Maniak003/DoZer/Documents/DoZer-current.png

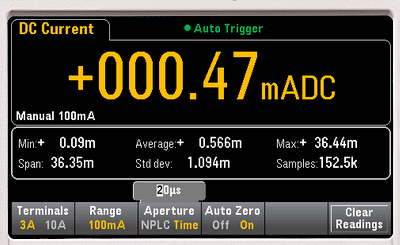
Documents/DoZer-current.png
