Maniak003/DoZer/Documents/DoZer_FSC-BT691.png

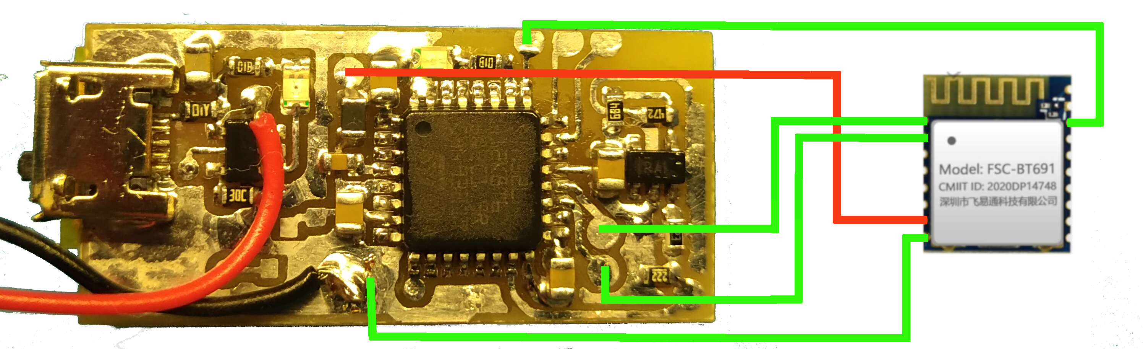
Documents/DoZer_FSC-BT691.png
