Maniak003/DoZer/Documents/IMG_20220416_122035.jpg

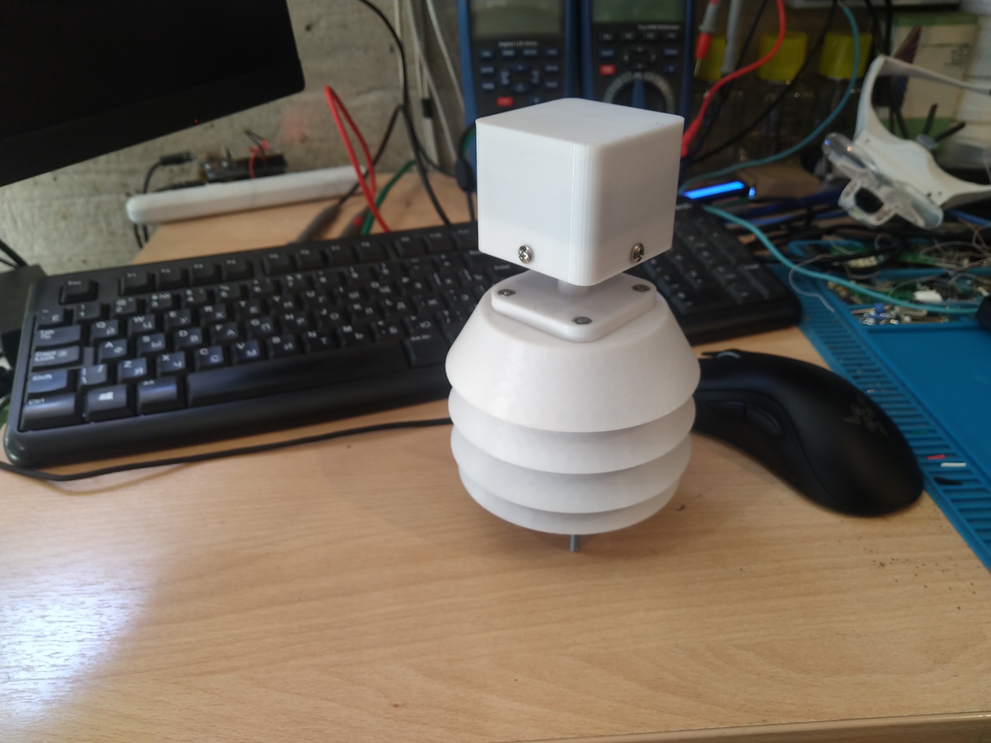
Documents/IMG_20220416_122035.jpg
