Maniak003/DoZer/Documents/LT8410-current.png

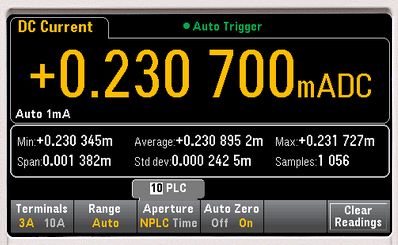
Documents/LT8410-current.png
