Maniak003/DoZer/Documents/Screenshot_20221201-142426.png

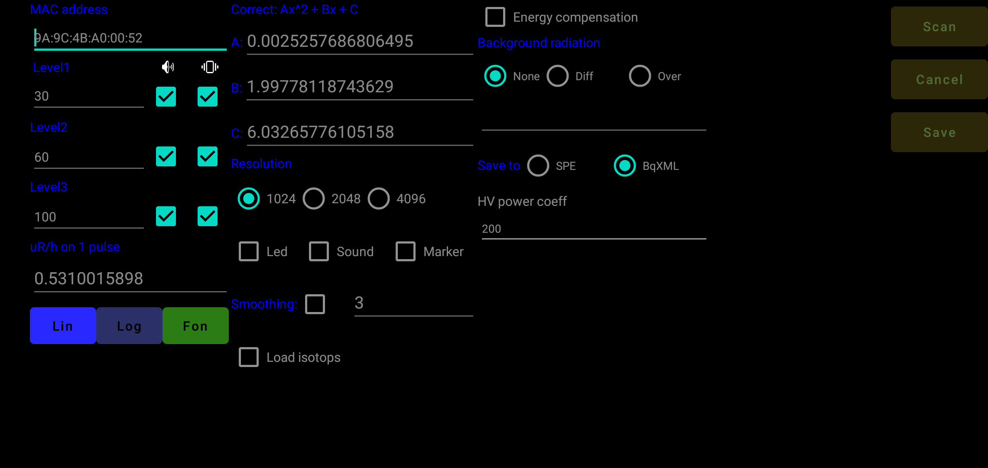
Documents/Screenshot_20221201-142426.png
