Maniak003/DoZer/picture/2023_03_03_14_29_00_972.png

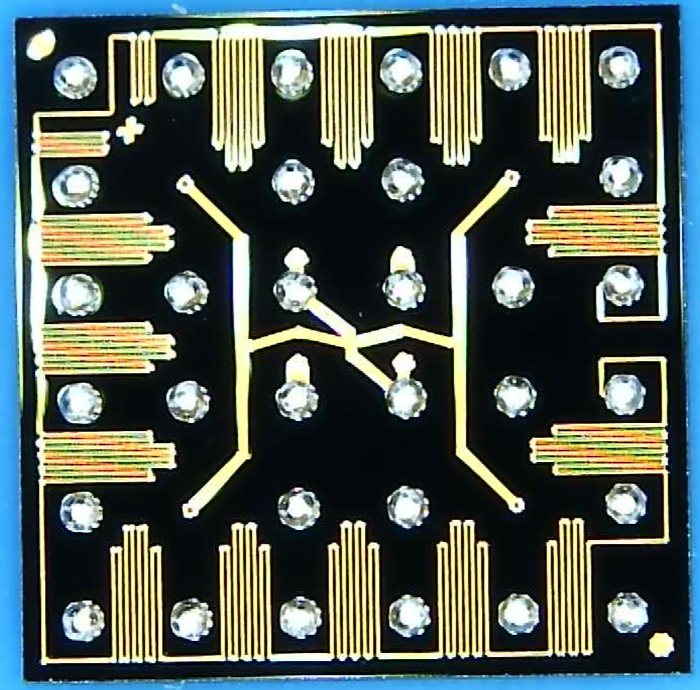
picture/2023_03_03_14_29_00_972.png
