Maniak003/DoZer/picture/2023_03_03_14_31_07_471.png

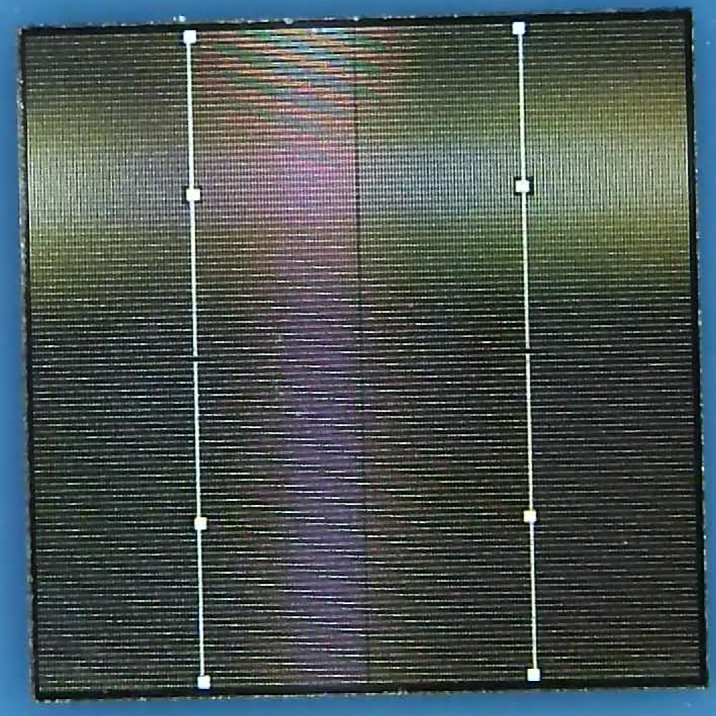
picture/2023_03_03_14_31_07_471.png
