Maniak003/DoZer/picture/DoZer_JDY-19.png

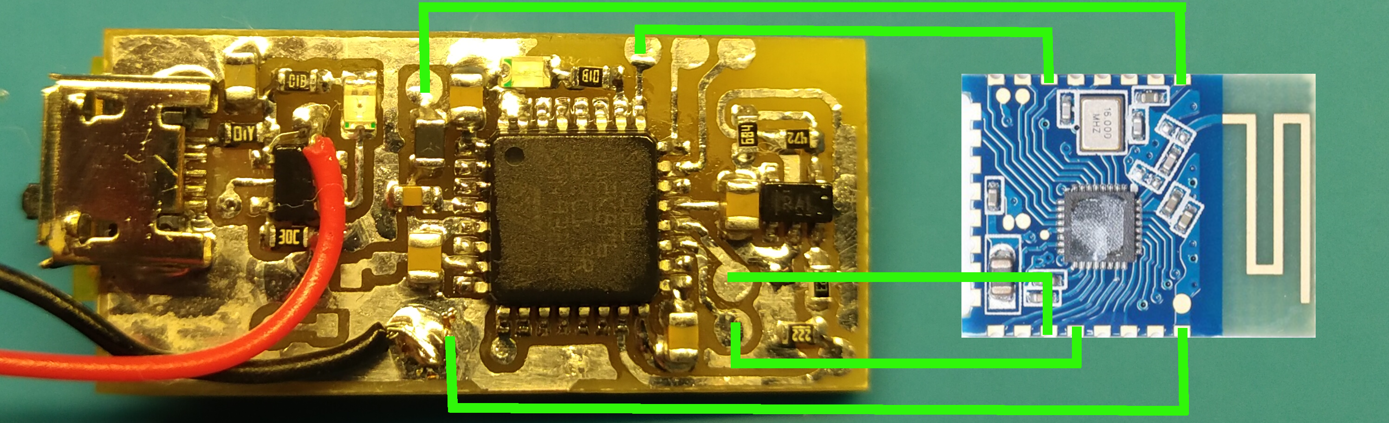
picture/DoZer_JDY-19.png
