Maniak003/DoZer/picture/IMG_20200828_080617.jpg

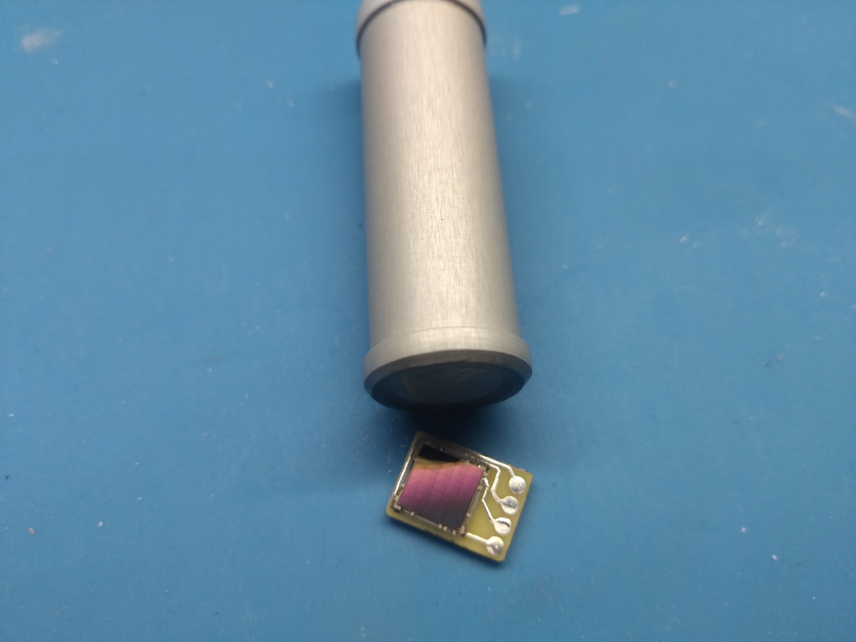
picture/IMG_20200828_080617.jpg
