Maniak003/DoZer/picture/IMG_20201008_110059.jpg

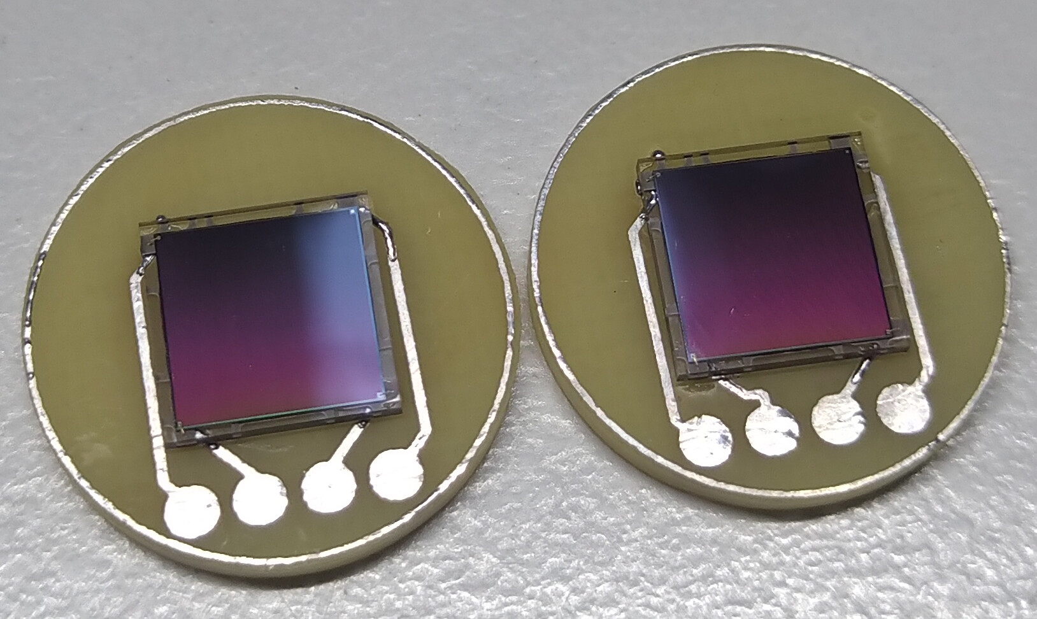
picture/IMG_20201008_110059.jpg
