Maniak003/DoZer/picture/IMG_20201029_205514.jpg

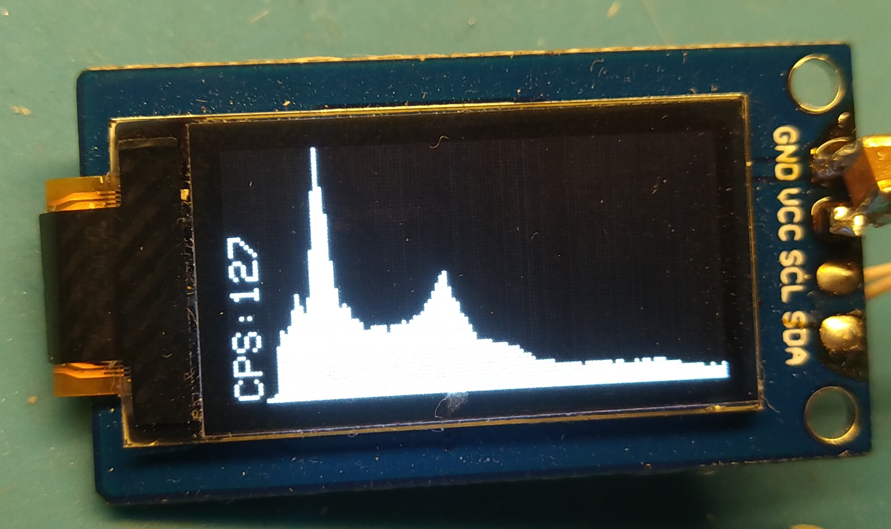
picture/IMG_20201029_205514.jpg
