Maniak003/DoZer/picture/IMG_20201205_212949.jpg

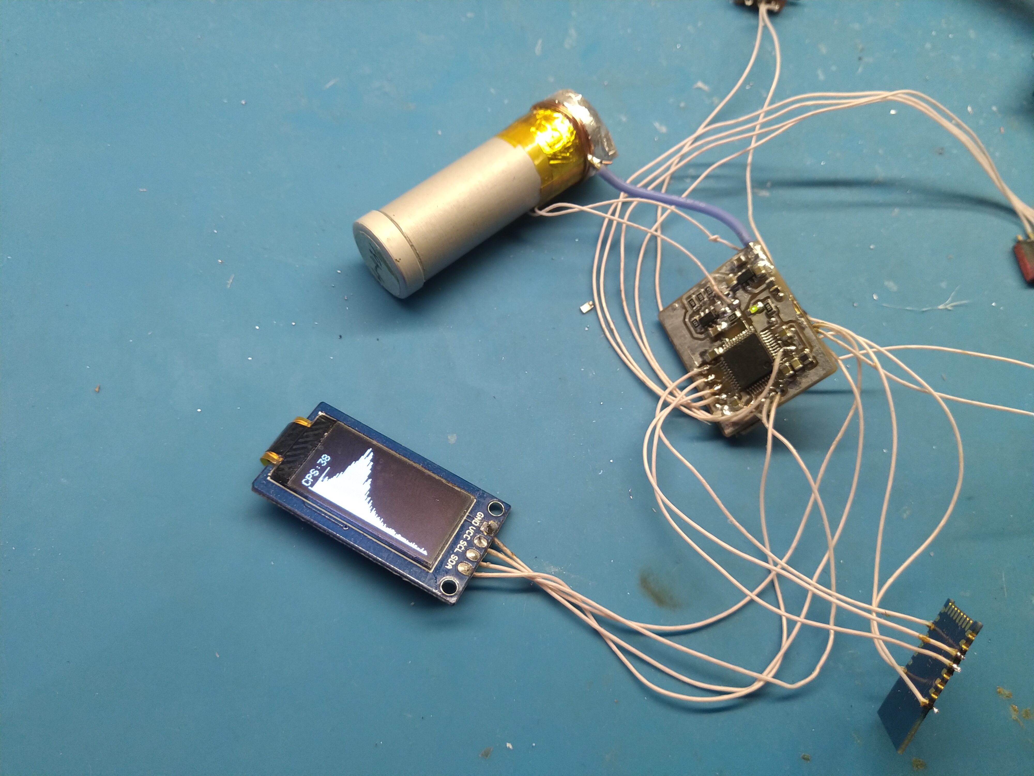
picture/IMG_20201205_212949.jpg
