Maniak003/DoZer/picture/IMG_20201224_195748.jpg

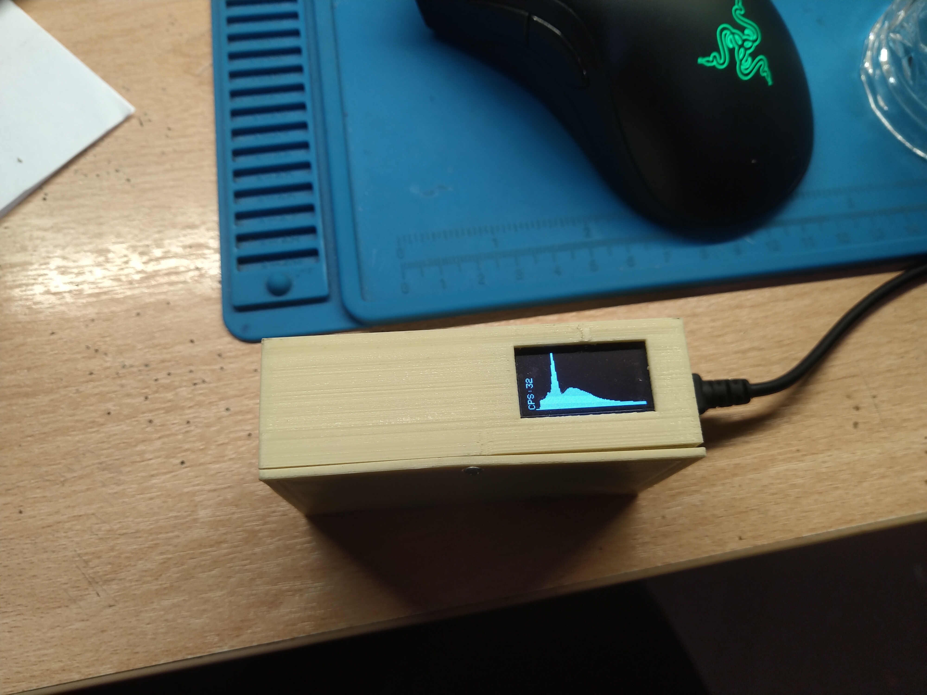
picture/IMG_20201224_195748.jpg
