Maniak003/DoZer/picture/IMG_20210123_151214.jpg

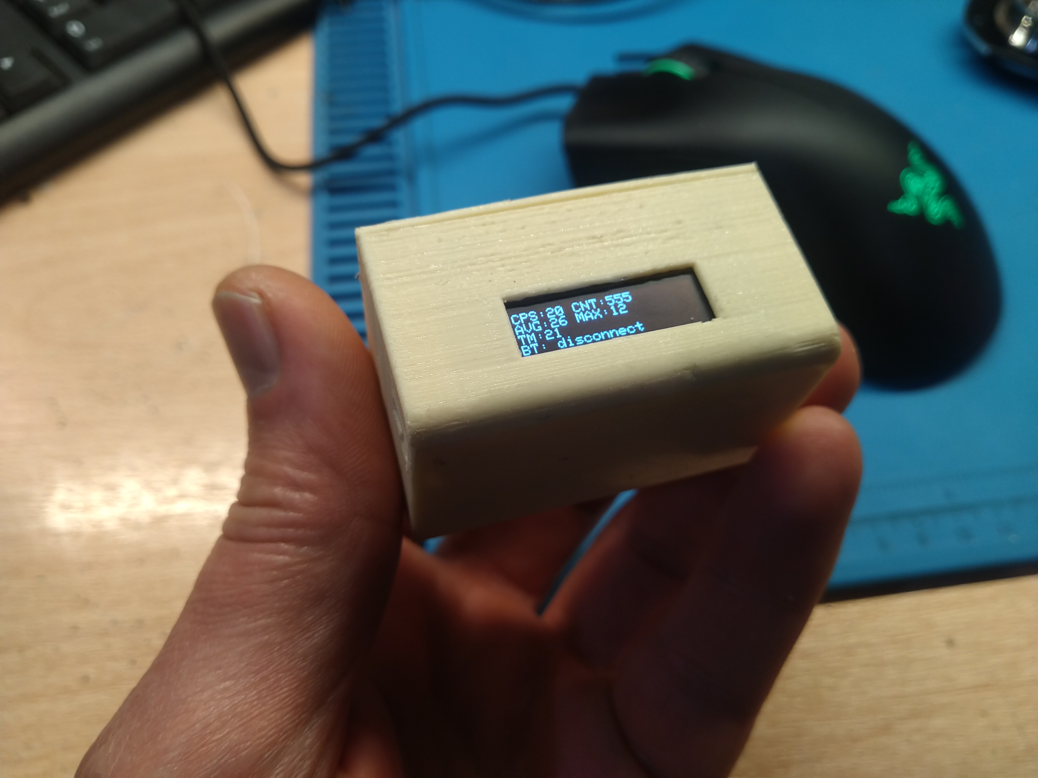
picture/IMG_20210123_151214.jpg
