Maniak003/DoZer/picture/IMG_20210207_145107.jpg

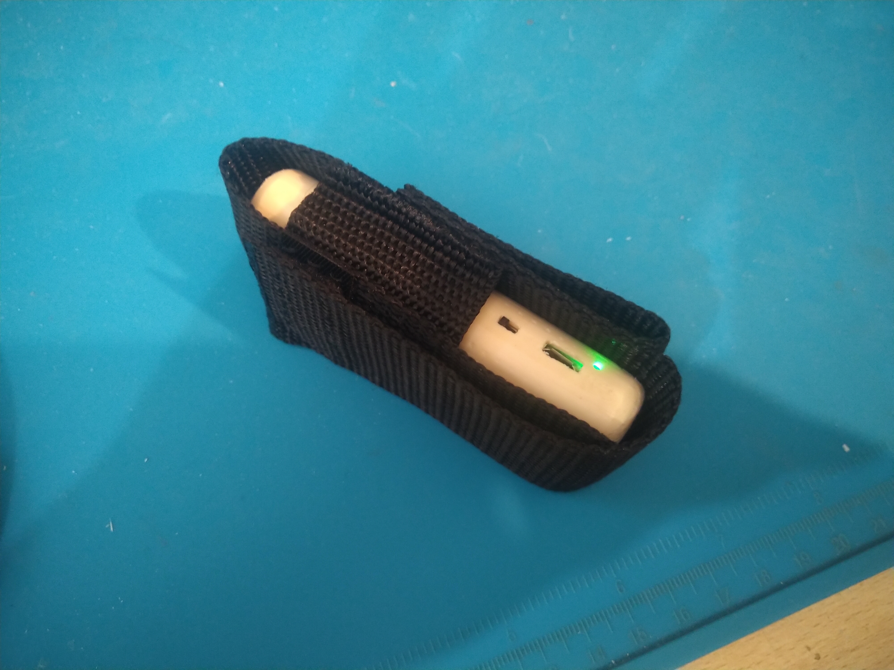
picture/IMG_20210207_145107.jpg
