Maniak003/DoZer/picture/IMG_20210209_133956.jpg

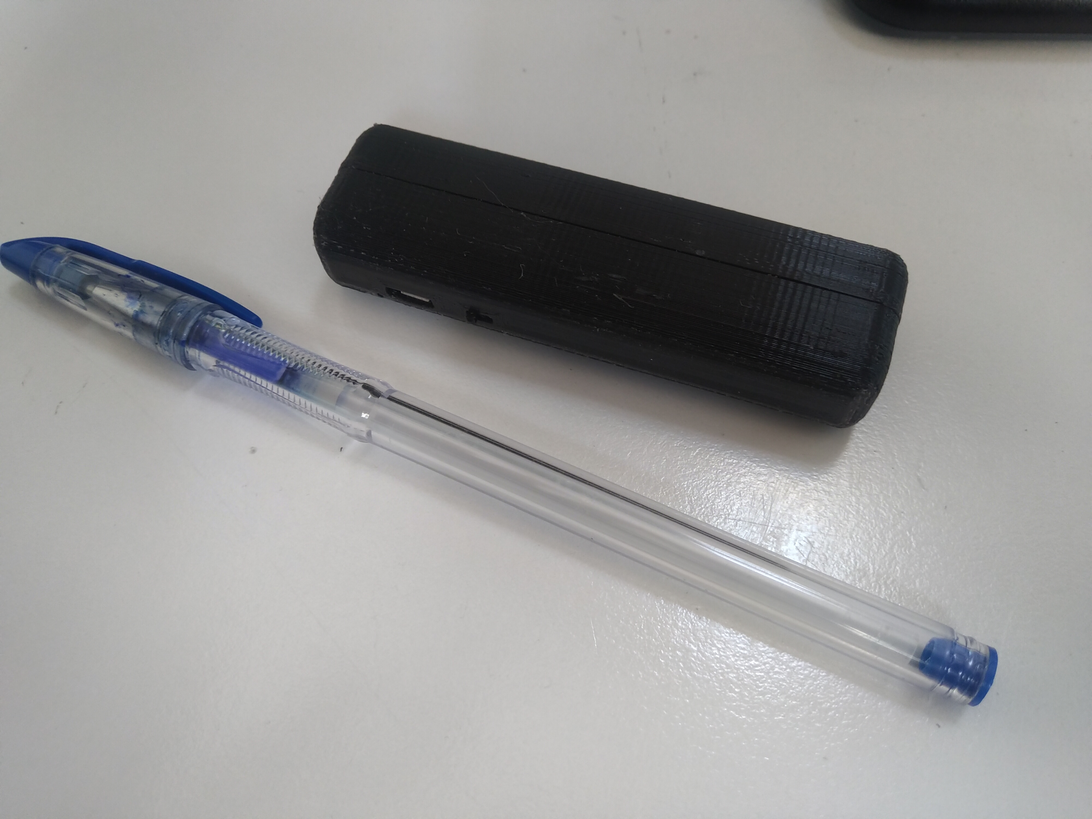
picture/IMG_20210209_133956.jpg
