Maniak003/DoZer/picture/IMG_20210417_190906.jpg

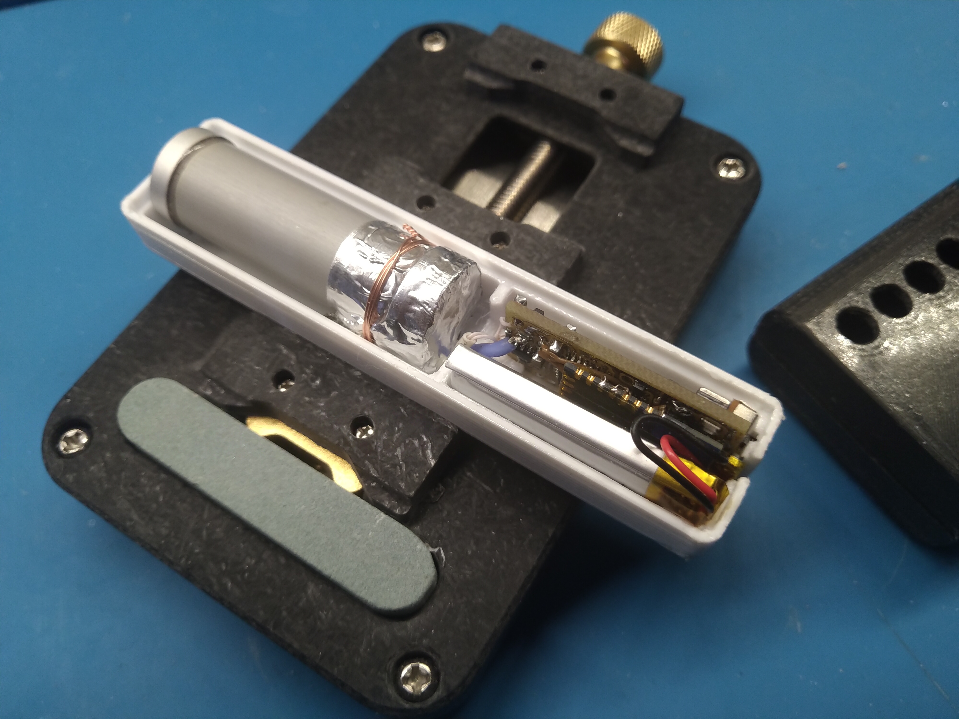
picture/IMG_20210417_190906.jpg
