Maniak003/DoZer/picture/IMG_20210417_202949.jpg

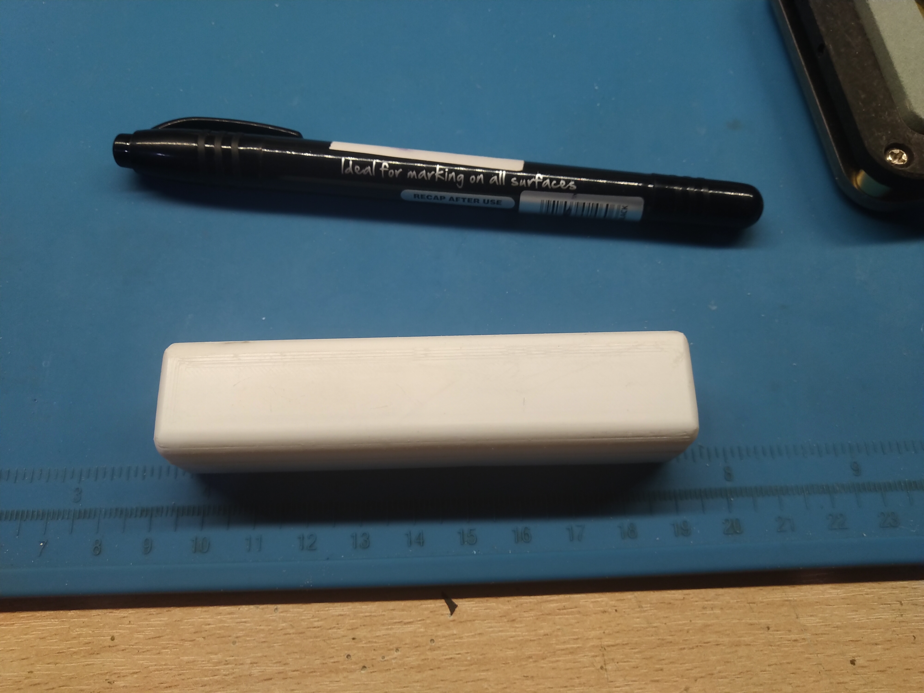
picture/IMG_20210417_202949.jpg
