Maniak003/DoZer/picture/IMG_20210425_131545.jpg

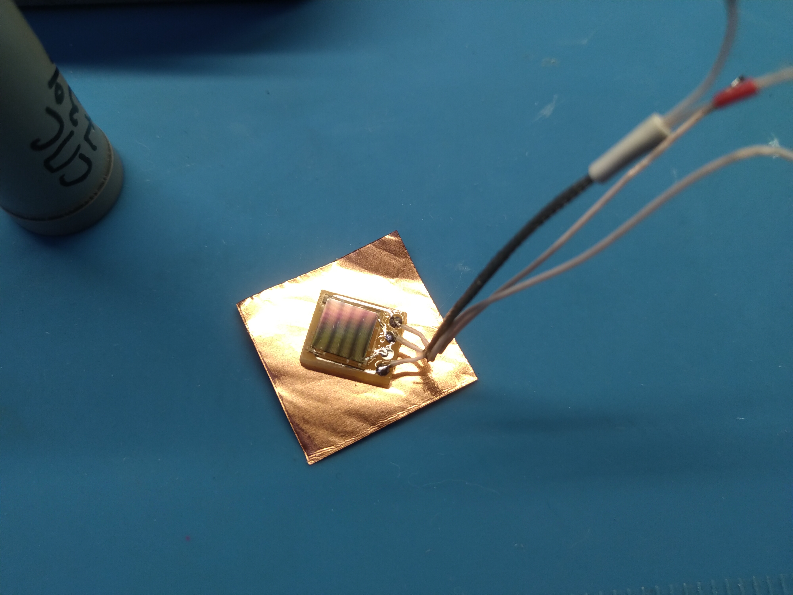
picture/IMG_20210425_131545.jpg
