Maniak003/DoZer/picture/IMG_20210425_131629.jpg

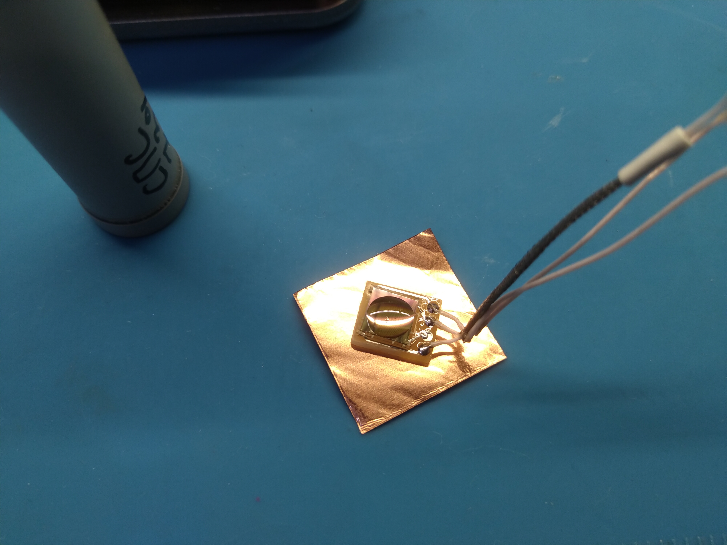
picture/IMG_20210425_131629.jpg
