Maniak003/DoZer/picture/IMG_20210425_131818.jpg

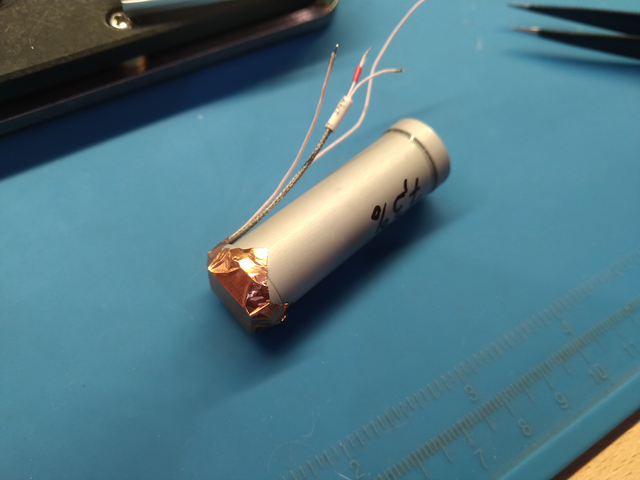
picture/IMG_20210425_131818.jpg
