Maniak003/DoZer/picture/IMG_20210425_132600.jpg

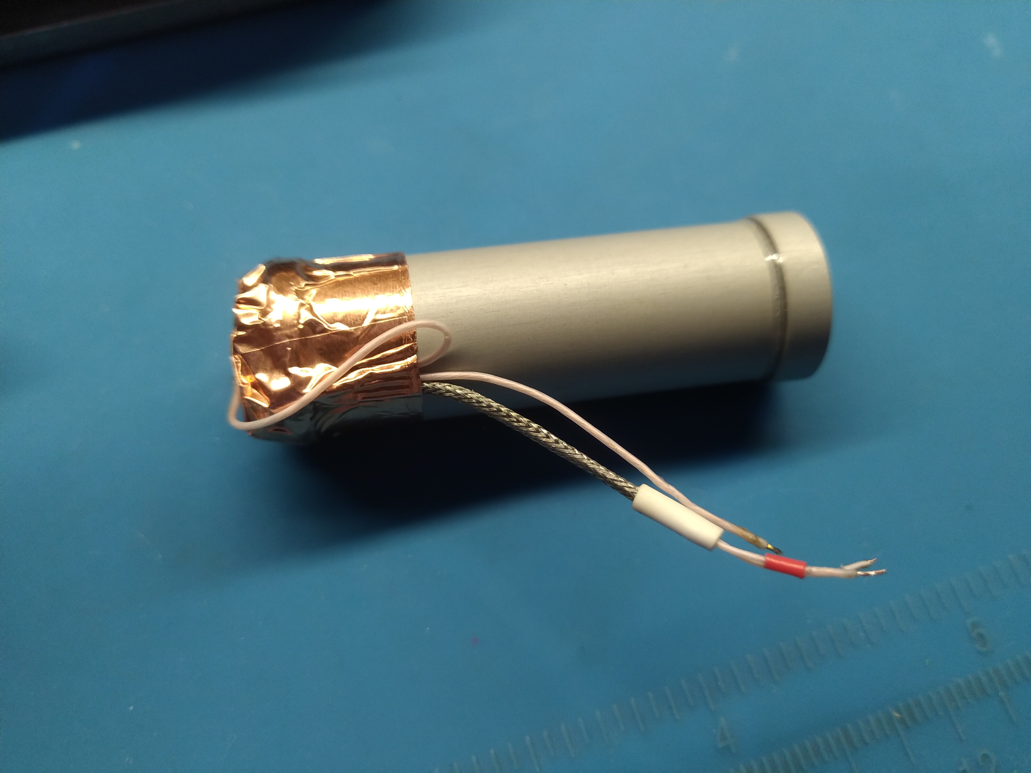
picture/IMG_20210425_132600.jpg
