Maniak003/DoZer/picture/IMG_20210530_200147.jpg

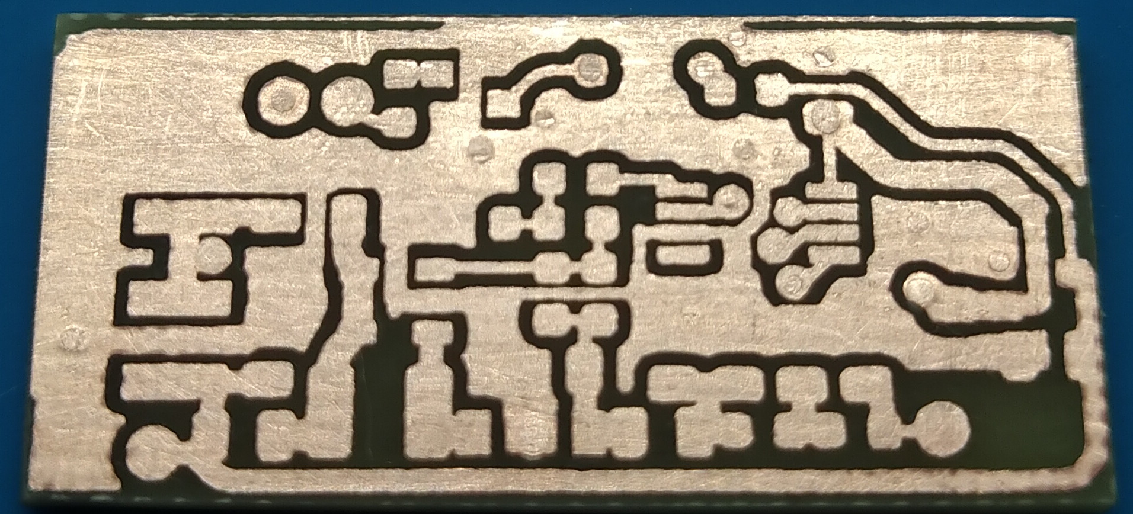
picture/IMG_20210530_200147.jpg
