Maniak003/DoZer/picture/IMG_20210530_200202.jpg

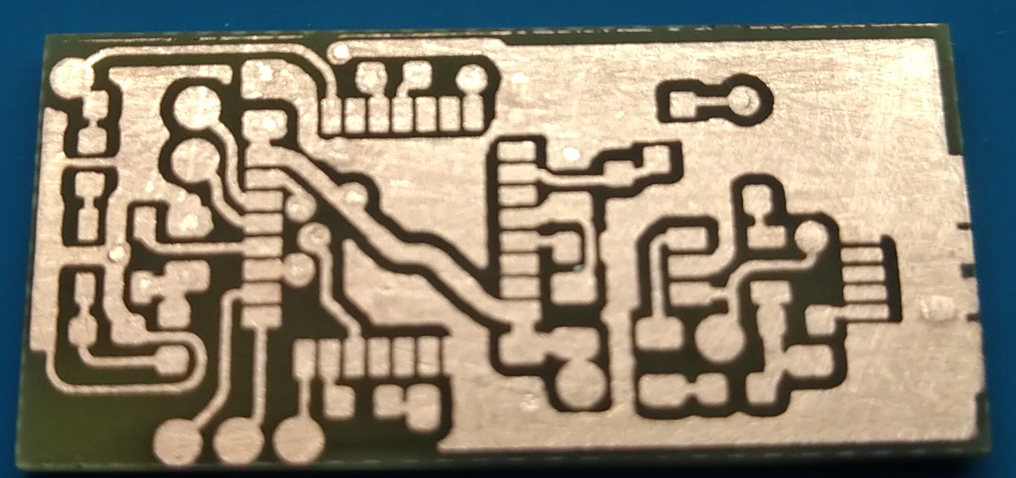
picture/IMG_20210530_200202.jpg
