Maniak003/DoZer/picture/IMG_20210603_091119_317.jpg

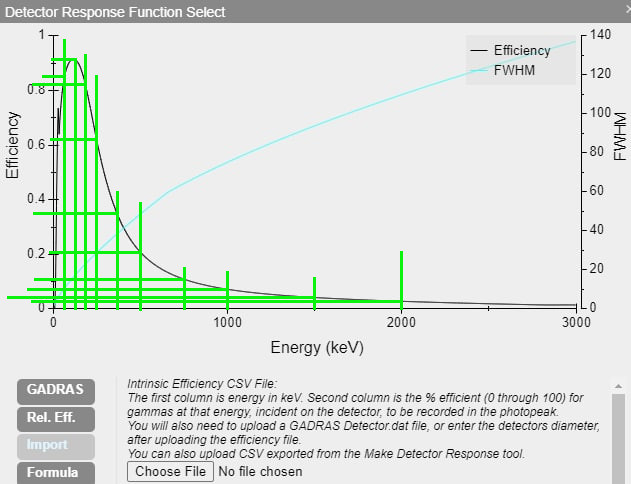
picture/IMG_20210603_091119_317.jpg
