Maniak003/DoZer/picture/IMG_20210627_105556.jpg

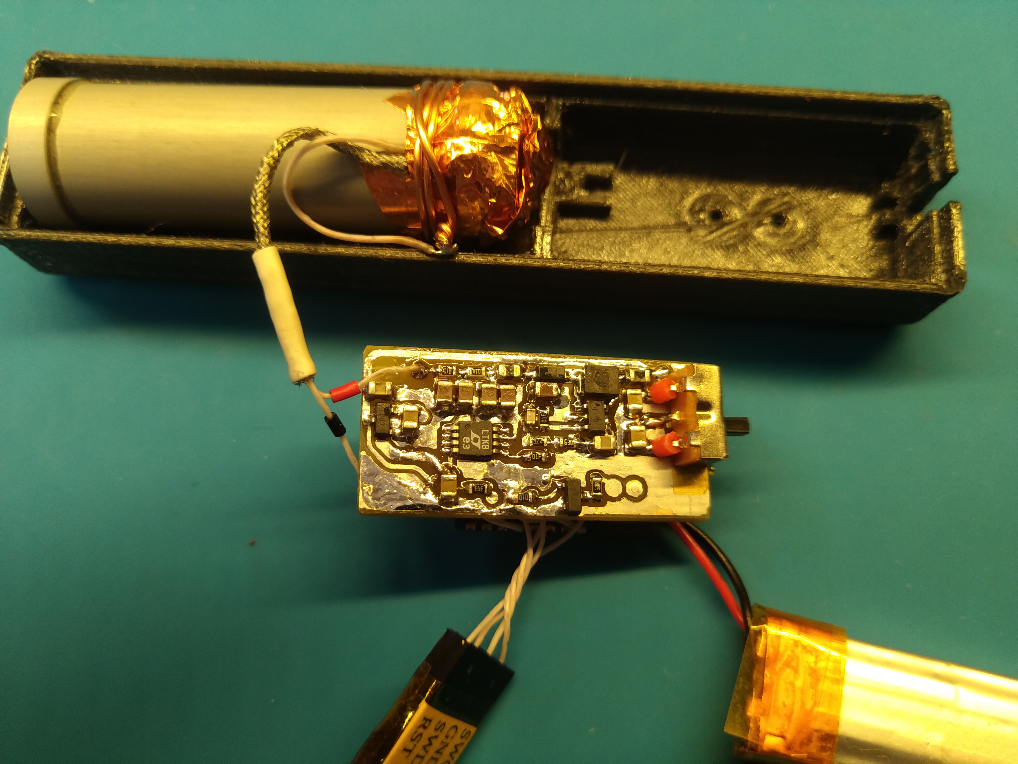
picture/IMG_20210627_105556.jpg
