Maniak003/DoZer/picture/IMG_20210627_110533.jpg

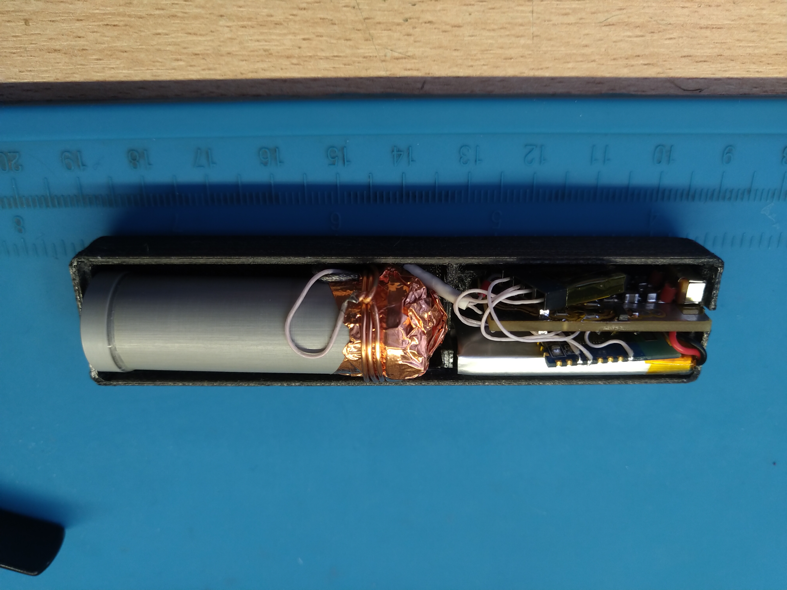
picture/IMG_20210627_110533.jpg
