Maniak003/DoZer/picture/IMG_20210627_110743.jpg

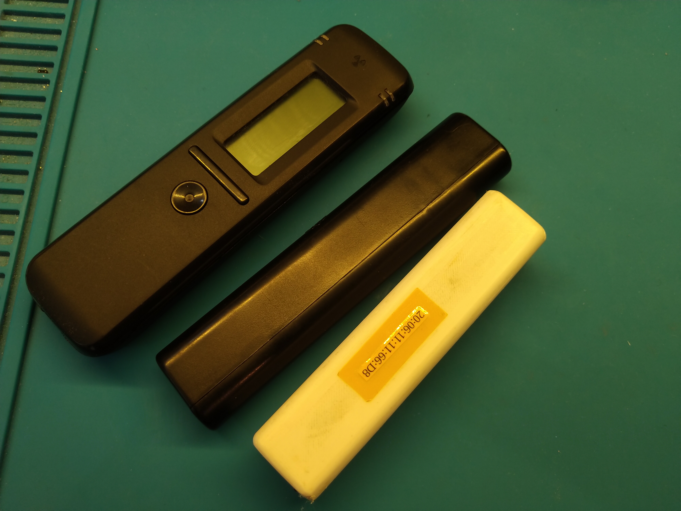
picture/IMG_20210627_110743.jpg
