Maniak003/DoZer/picture/IMG_20210912_121010.jpg

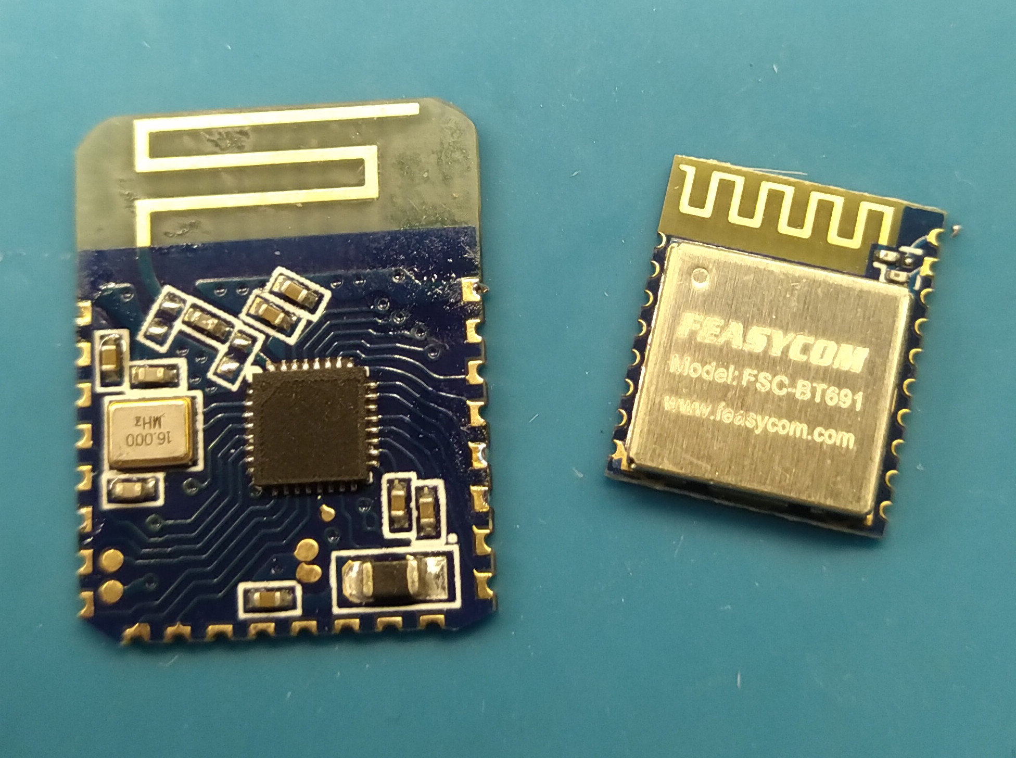
picture/IMG_20210912_121010.jpg
