Maniak003/DoZer/picture/IMG_20211003_150513.jpg

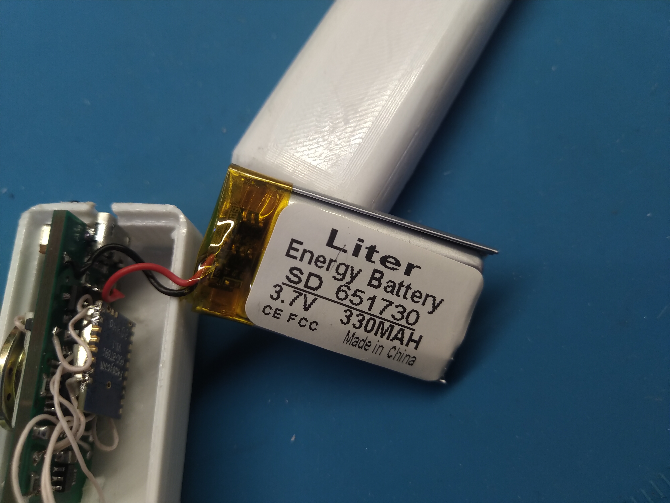
picture/IMG_20211003_150513.jpg
