Maniak003/DoZer/picture/IMG_20211003_150646.jpg

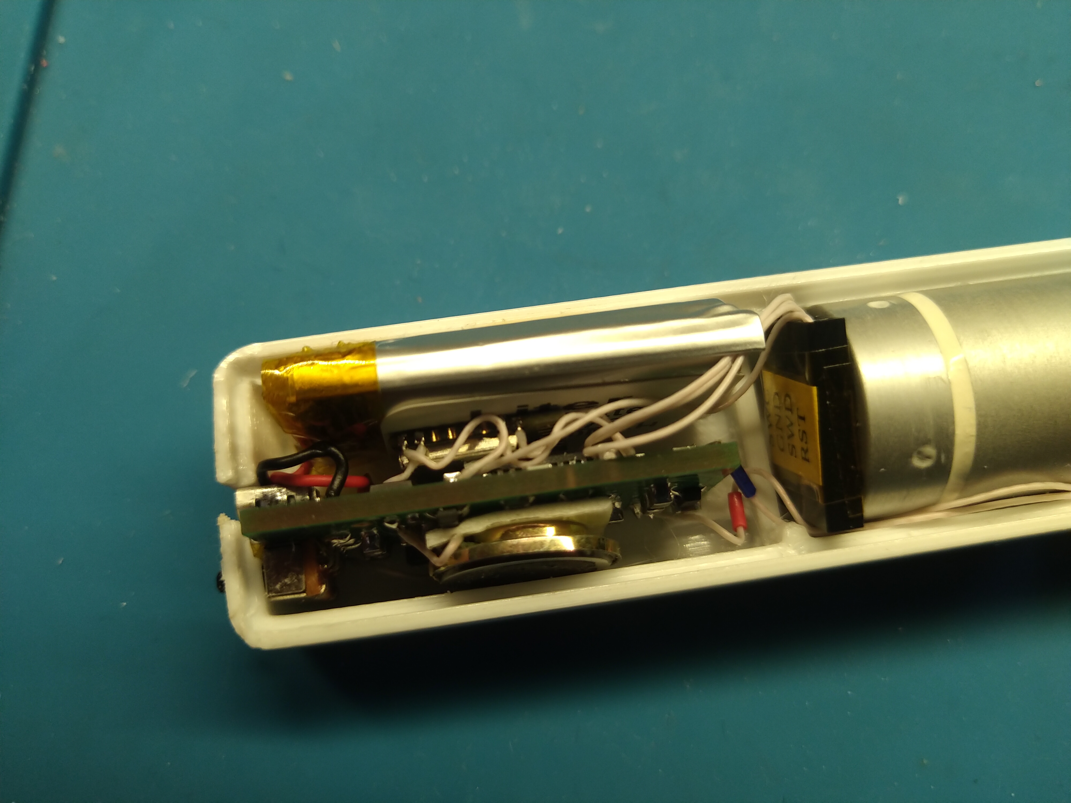
picture/IMG_20211003_150646.jpg
