Maniak003/DoZer/picture/IMG_20211007_115434.jpg

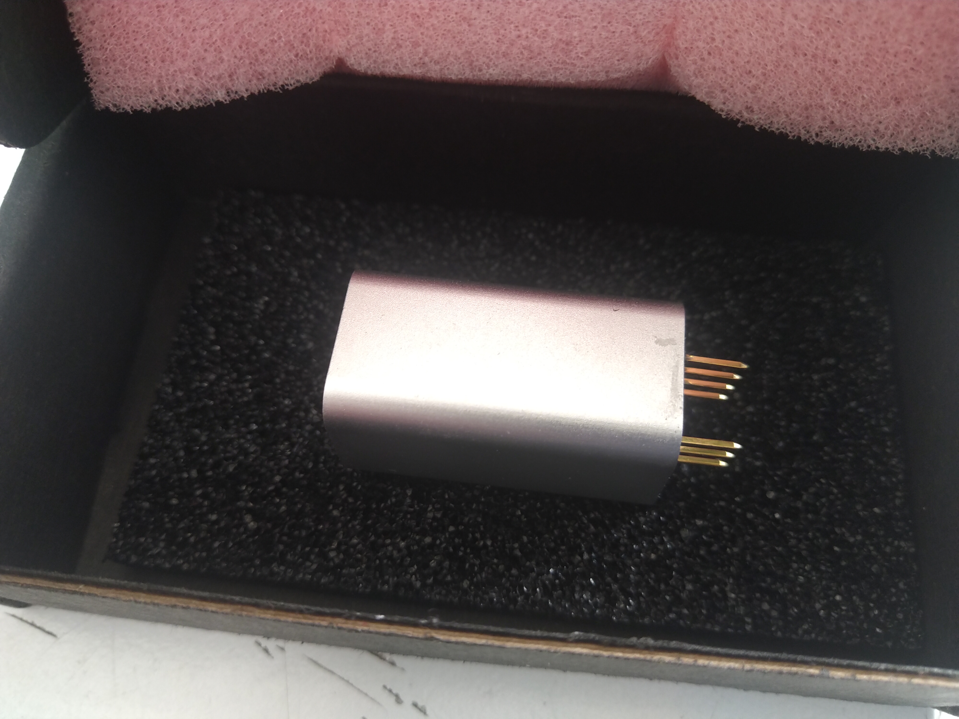
picture/IMG_20211007_115434.jpg
