Maniak003/DoZer/picture/IMG_20211007_115442.jpg

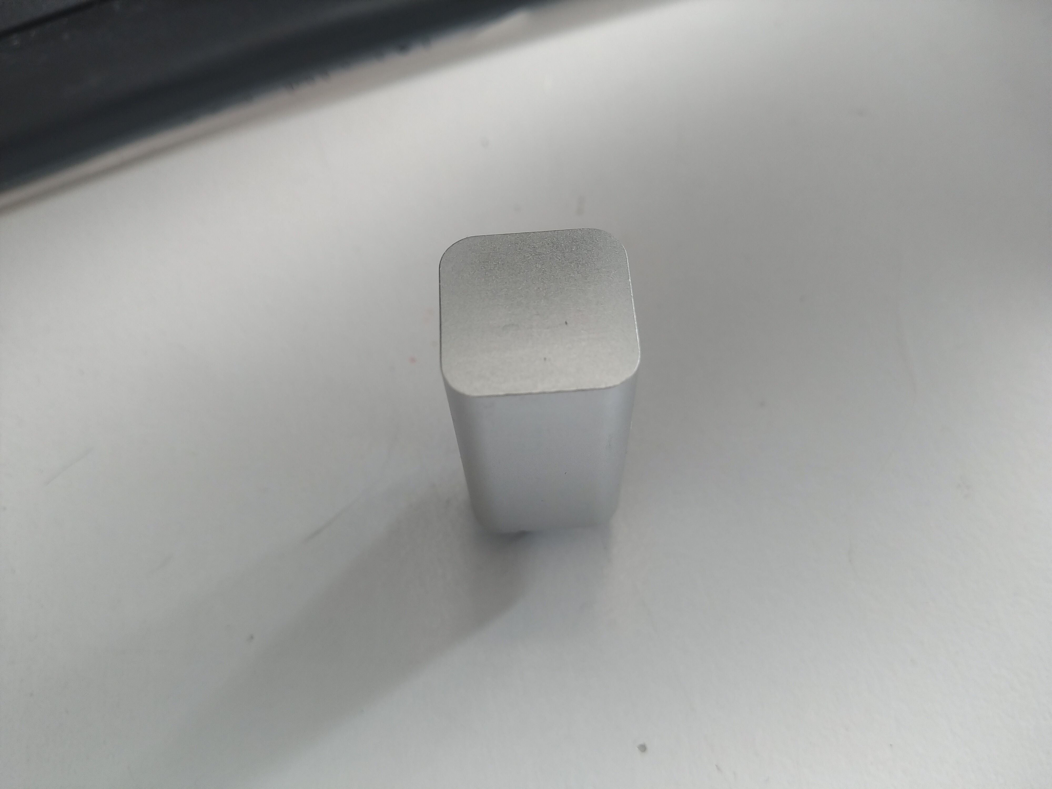
picture/IMG_20211007_115442.jpg
