Maniak003/DoZer/picture/IMG_20211007_115449.jpg

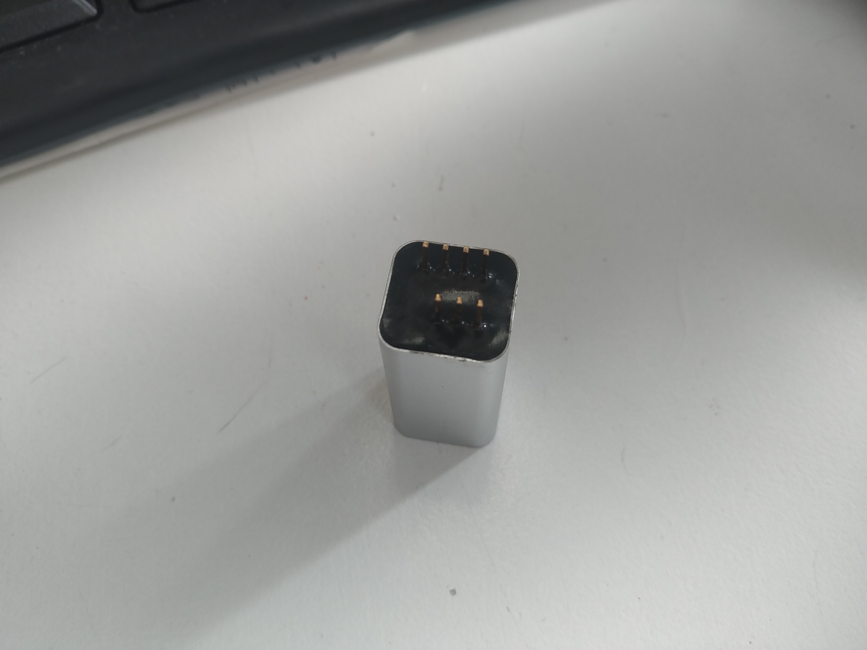
picture/IMG_20211007_115449.jpg
