Maniak003/DoZer/picture/IMG_20211007_120346.jpg

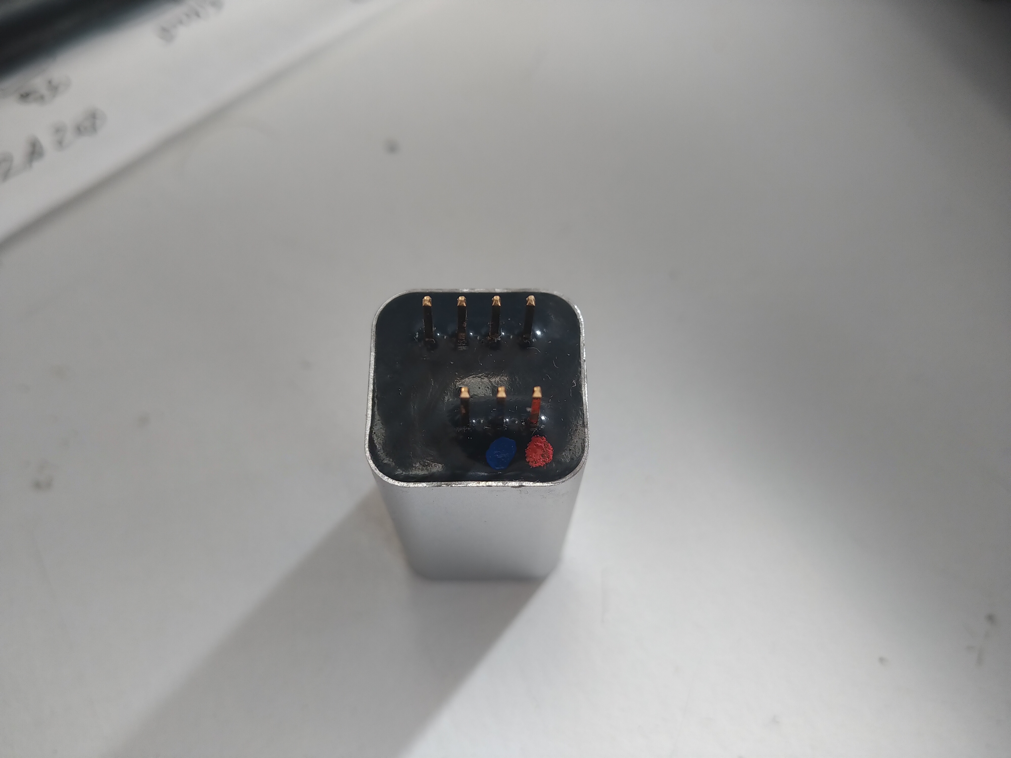
picture/IMG_20211007_120346.jpg
