Maniak003/DoZer/picture/IMG_20211010_180026.jpg

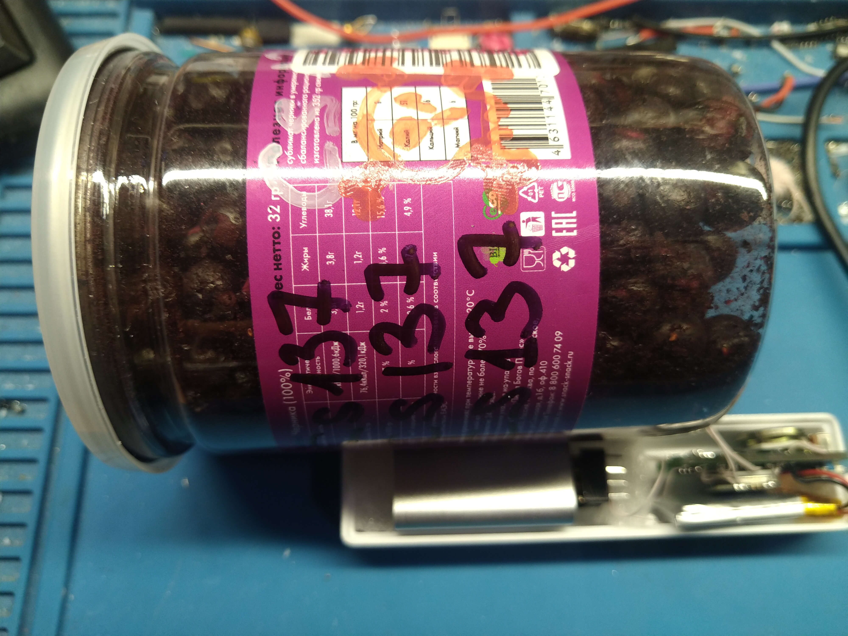
picture/IMG_20211010_180026.jpg
