Maniak003/DoZer/picture/IMG_20211022_104003.jpg

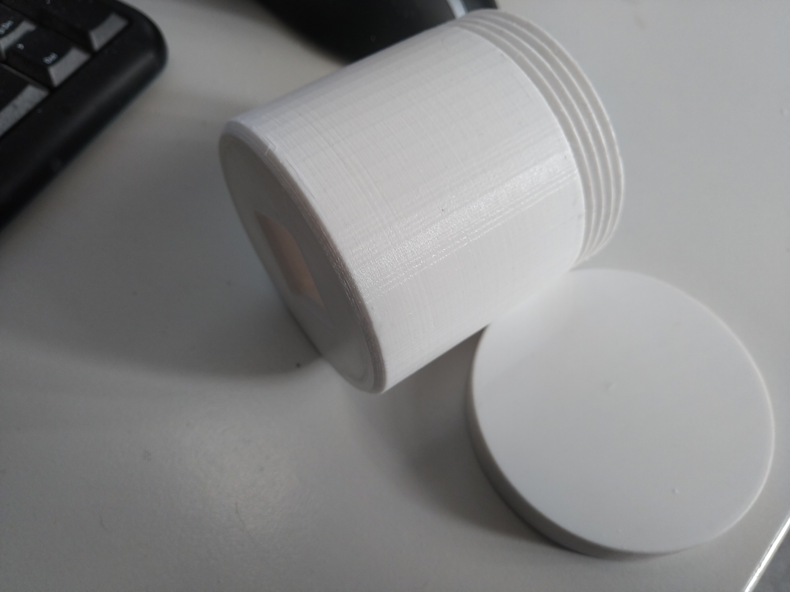
picture/IMG_20211022_104003.jpg
