Maniak003/DoZer/picture/IMG_20211022_104049.jpg

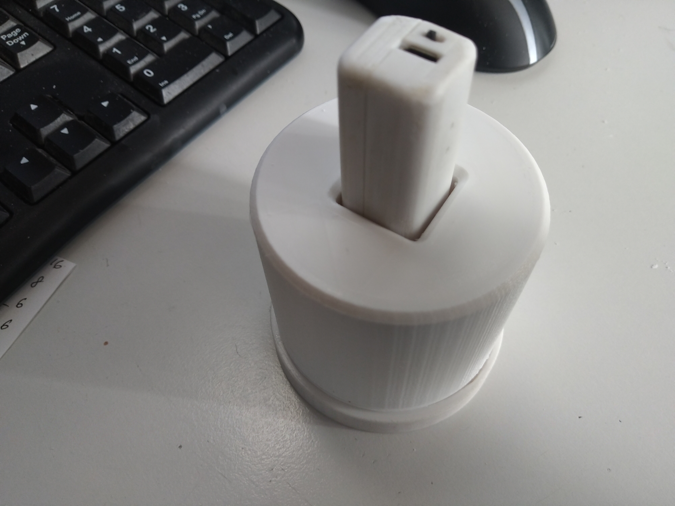
picture/IMG_20211022_104049.jpg
