Maniak003/DoZer/picture/IMG_20211115_132411.jpg

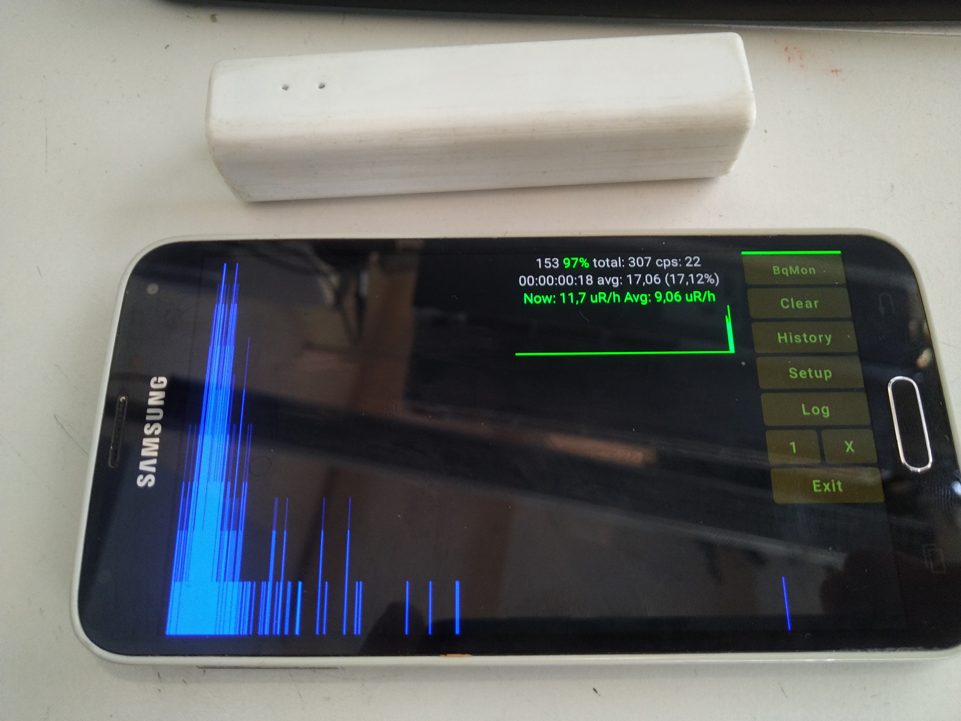
picture/IMG_20211115_132411.jpg
