Maniak003/DoZer/picture/IMG_20230303_142326.jpg

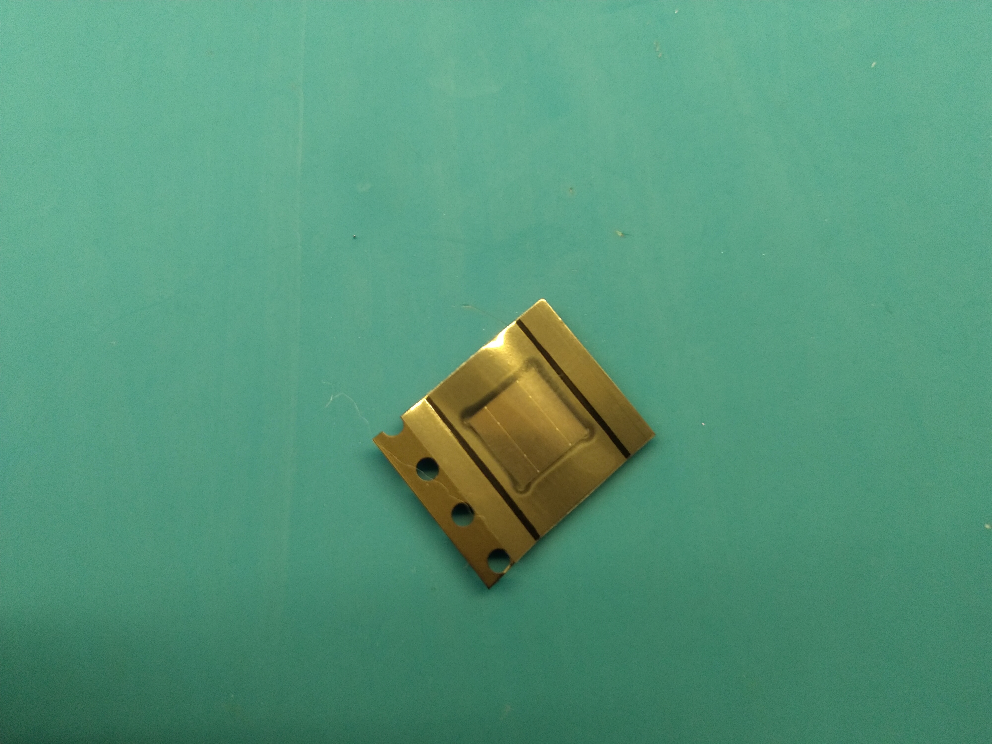
picture/IMG_20230303_142326.jpg
