Maniak003/DoZer/picture/IMG_20230303_142428.jpg

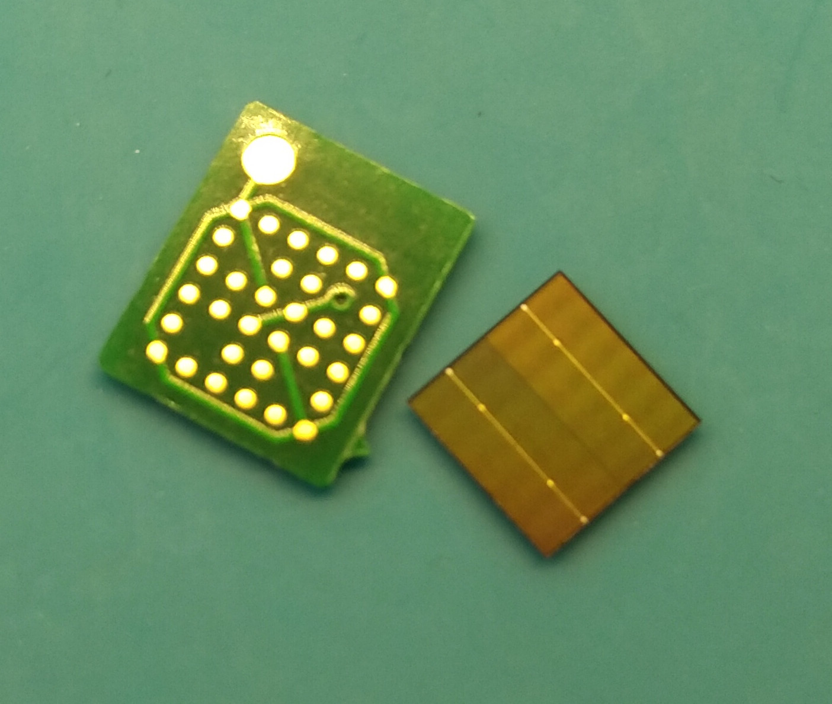
picture/IMG_20230303_142428.jpg
