Maniak003/DoZer/picture/IMG_20230303_151313.jpg

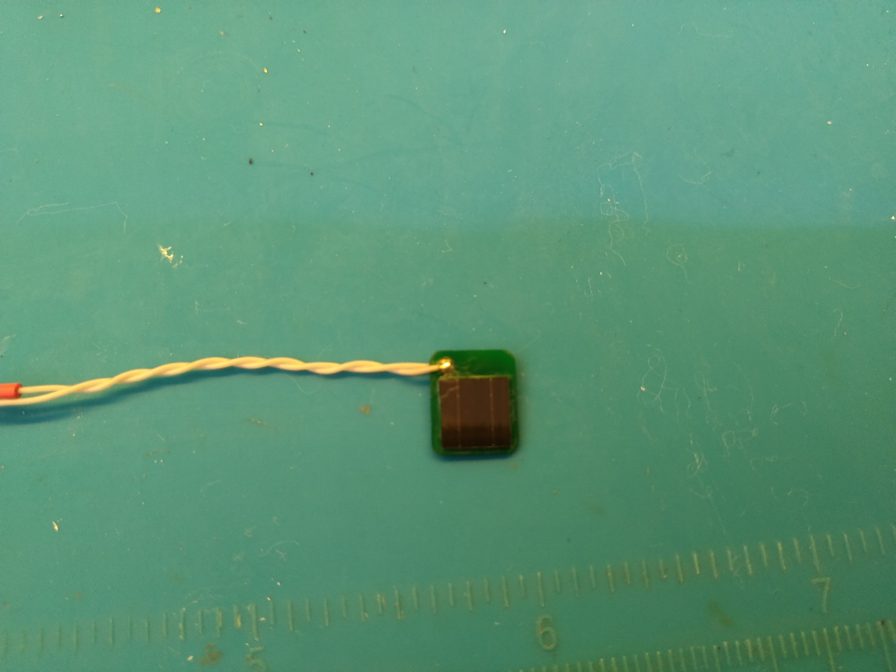
picture/IMG_20230303_151313.jpg
