Maniak003/DoZer/picture/IMG_20230303_152422.jpg

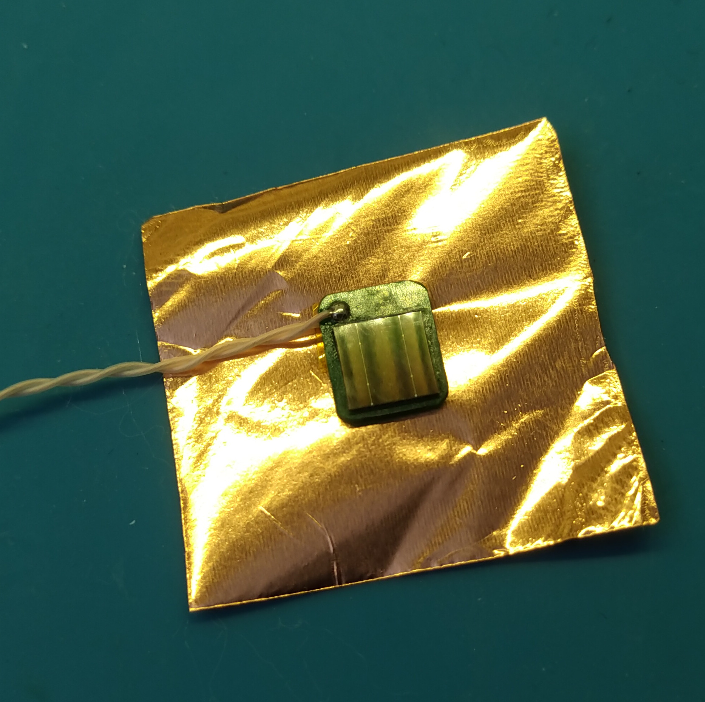
picture/IMG_20230303_152422.jpg
