Maniak003/DoZer/picture/IMG_20230303_153013.jpg

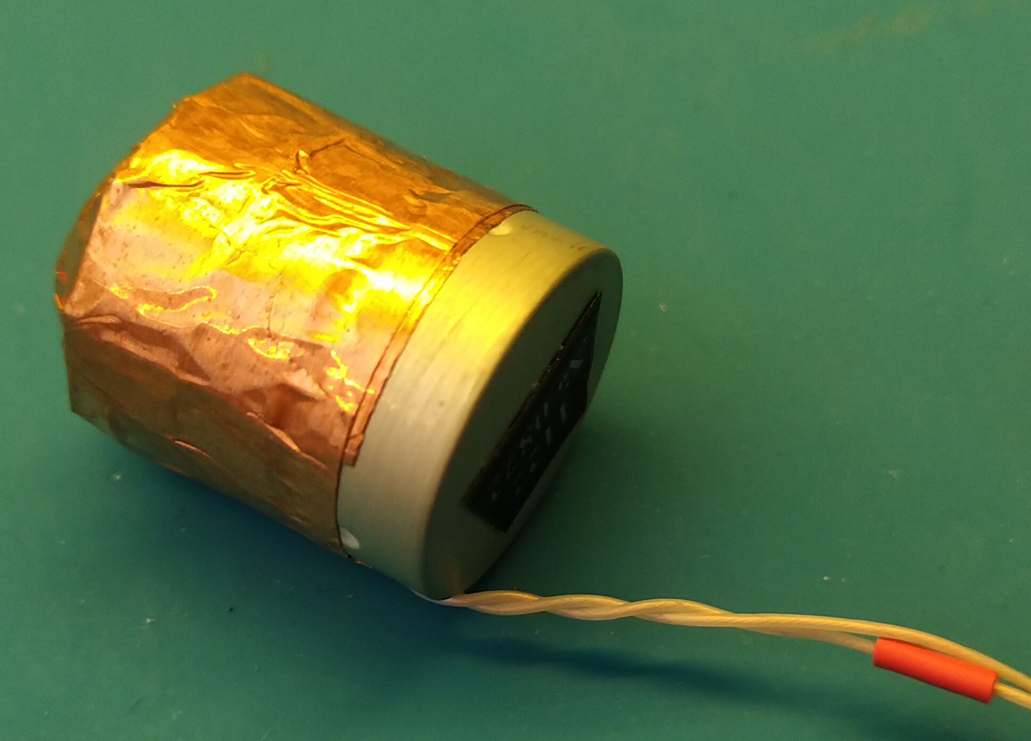
picture/IMG_20230303_153013.jpg
