Maniak003/DoZer/picture/IMG_20230303_201336.jpg

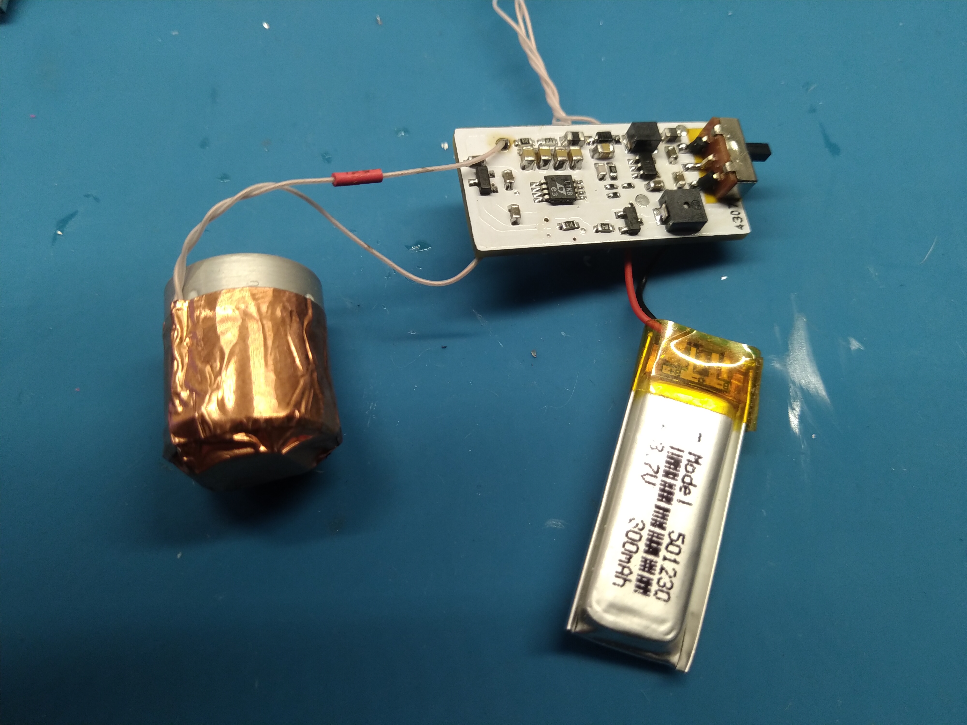
picture/IMG_20230303_201336.jpg
