Maniak003/DoZer/picture/SC-STM32L412K8.png

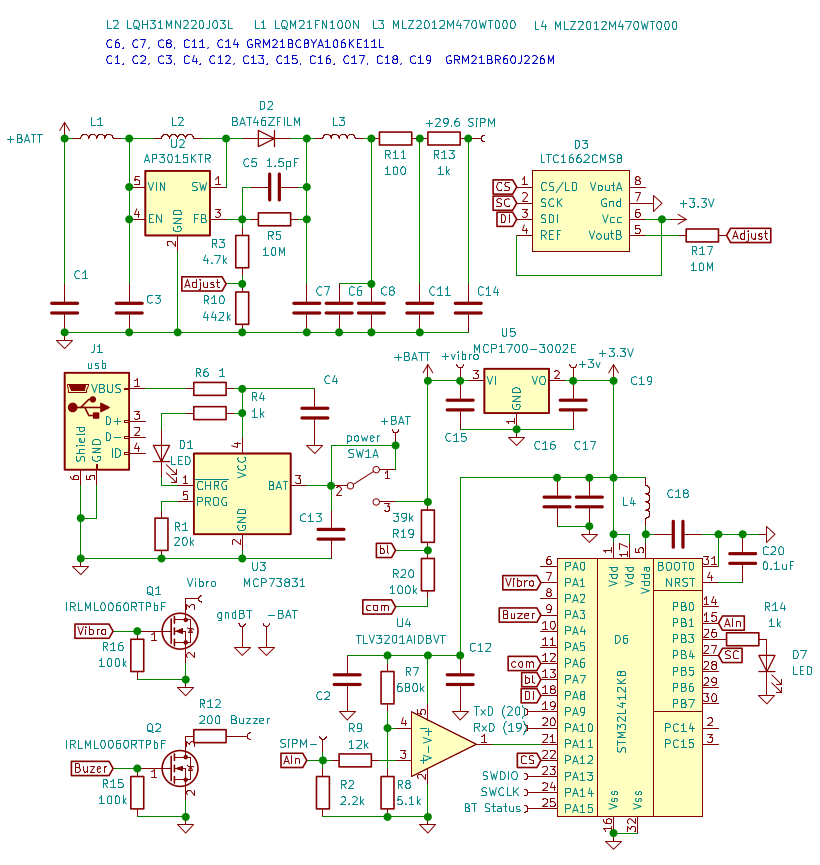
picture/SC-STM32L412K8.png
