Maniak003/DoZer/picture/scope_3.png

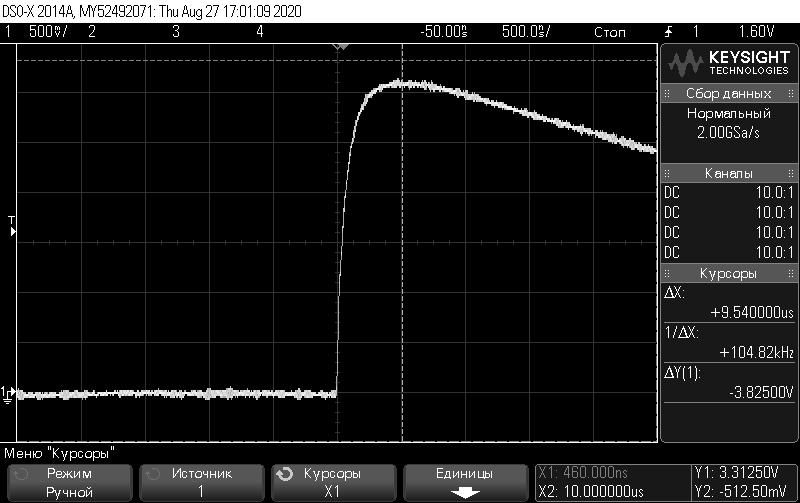
picture/scope_3.png
