Maniak003/DoZer/picture/Screenshot_20201224-195708.png

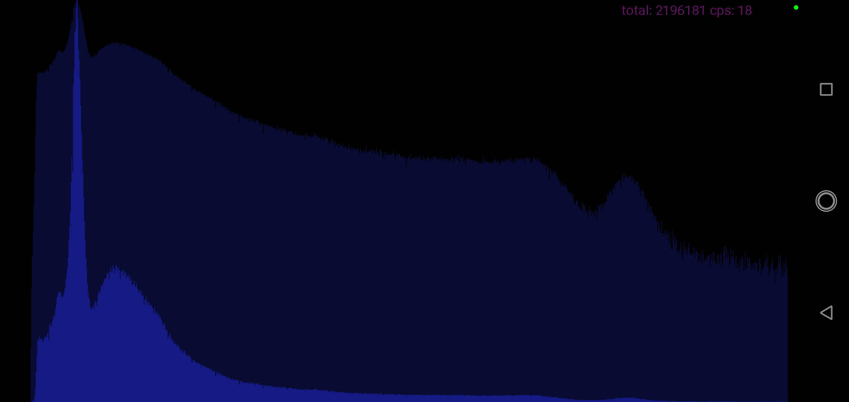
picture/Screenshot_20201224-195708.png
