Maniak003/DoZer/picture/Screenshot_20210227-133249.png

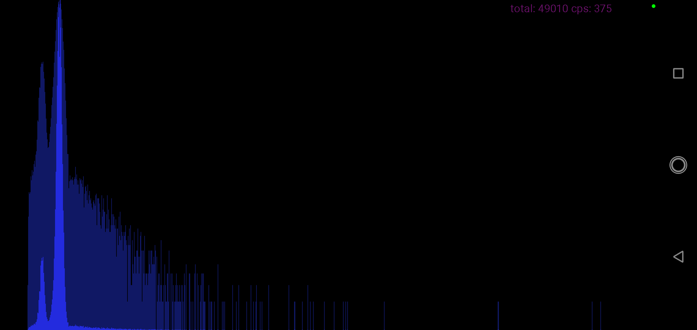
picture/Screenshot_20210227-133249.png
