Maniak003/DoZer/picture/Screenshot_20210227-202007.png

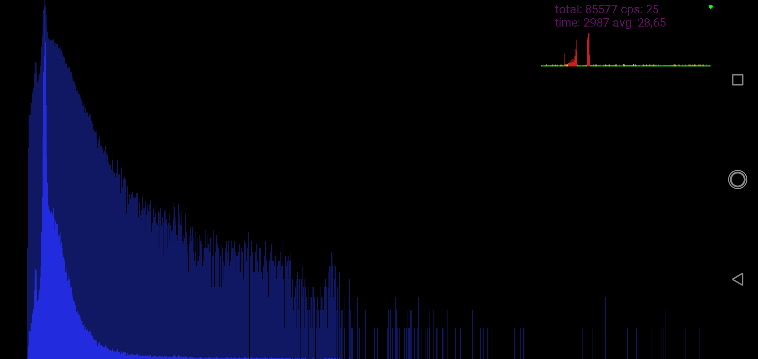
picture/Screenshot_20210227-202007.png
