Maniak003/DoZer/picture/Screenshot_20210418-202221.png

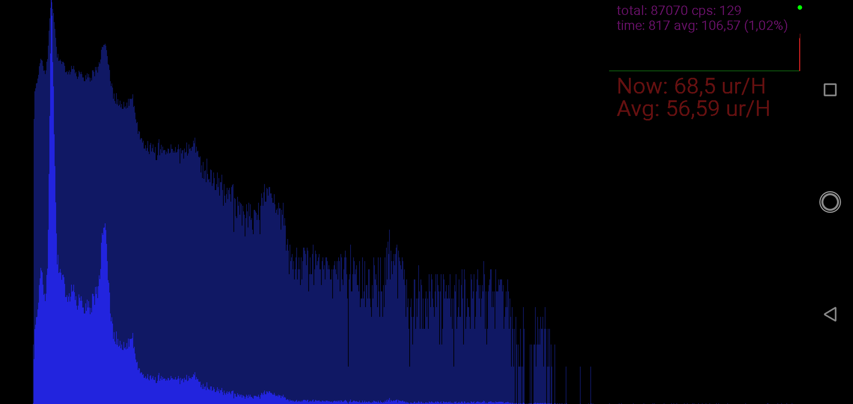
picture/Screenshot_20210418-202221.png
