Maniak003/DoZer/picture/Screenshot_20210519-121428.png

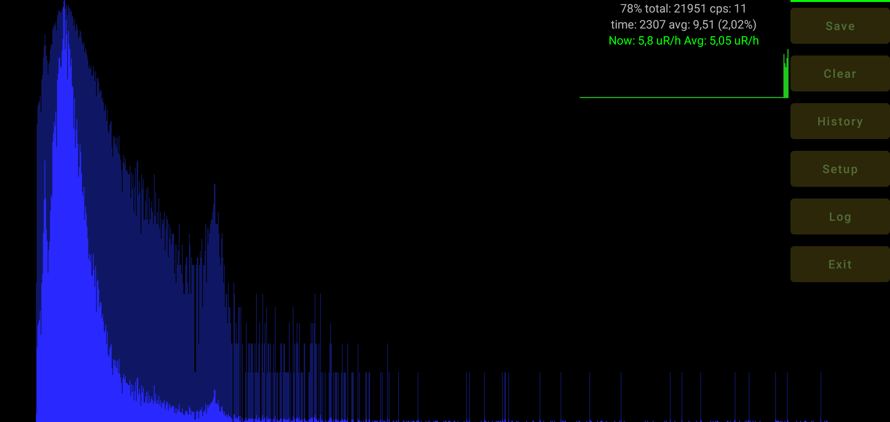
picture/Screenshot_20210519-121428.png
