Maniak003/DoZer/picture/Screenshot_20210606-102400.png

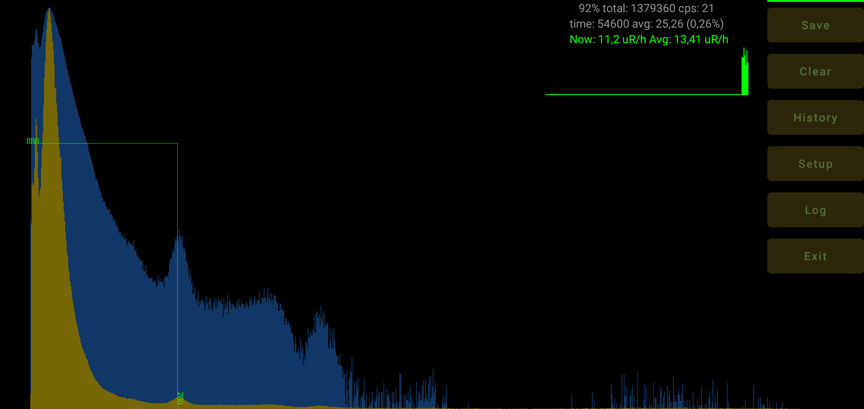
picture/Screenshot_20210606-102400.png
