Maniak003/DoZer/picture/Screenshot_20210606-123445.png

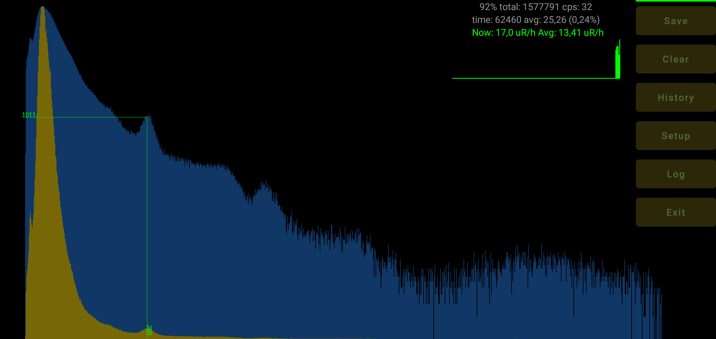
picture/Screenshot_20210606-123445.png
