Maniak003/DoZer/picture/Screenshot_20210607-130254.png

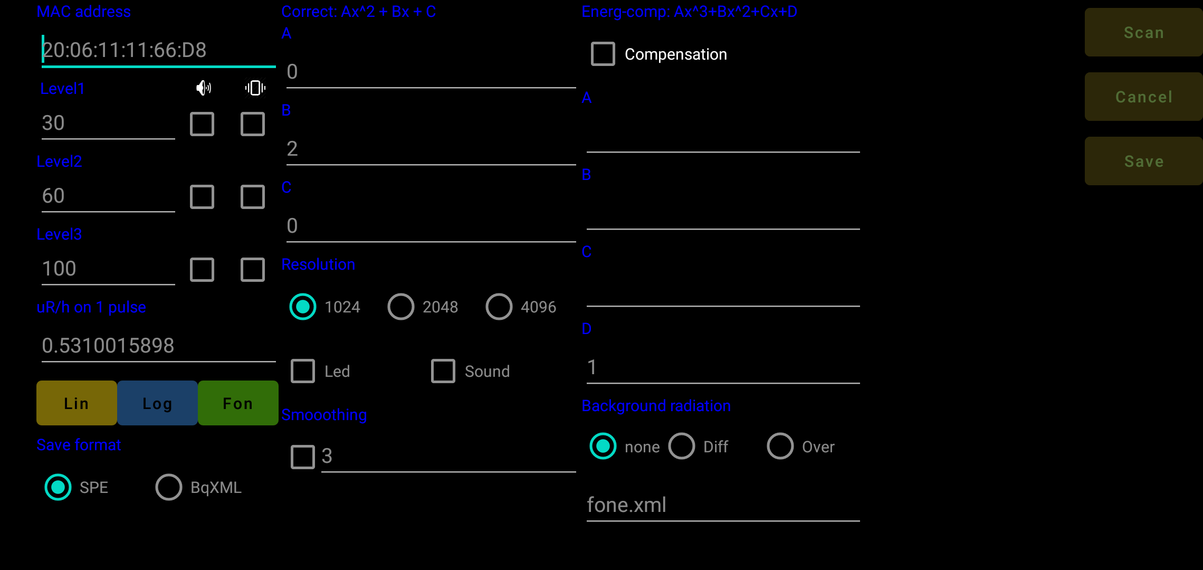
picture/Screenshot_20210607-130254.png
