Maniak003/DoZer/picture/Screenshot_20210608-120211.png

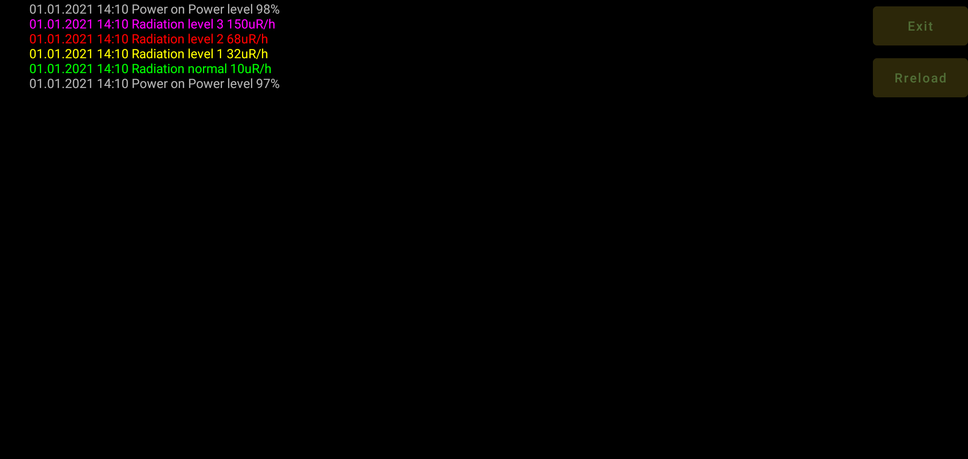
picture/Screenshot_20210608-120211.png
