Maniak003/DoZer/picture/Screenshot_20210627-153201.png

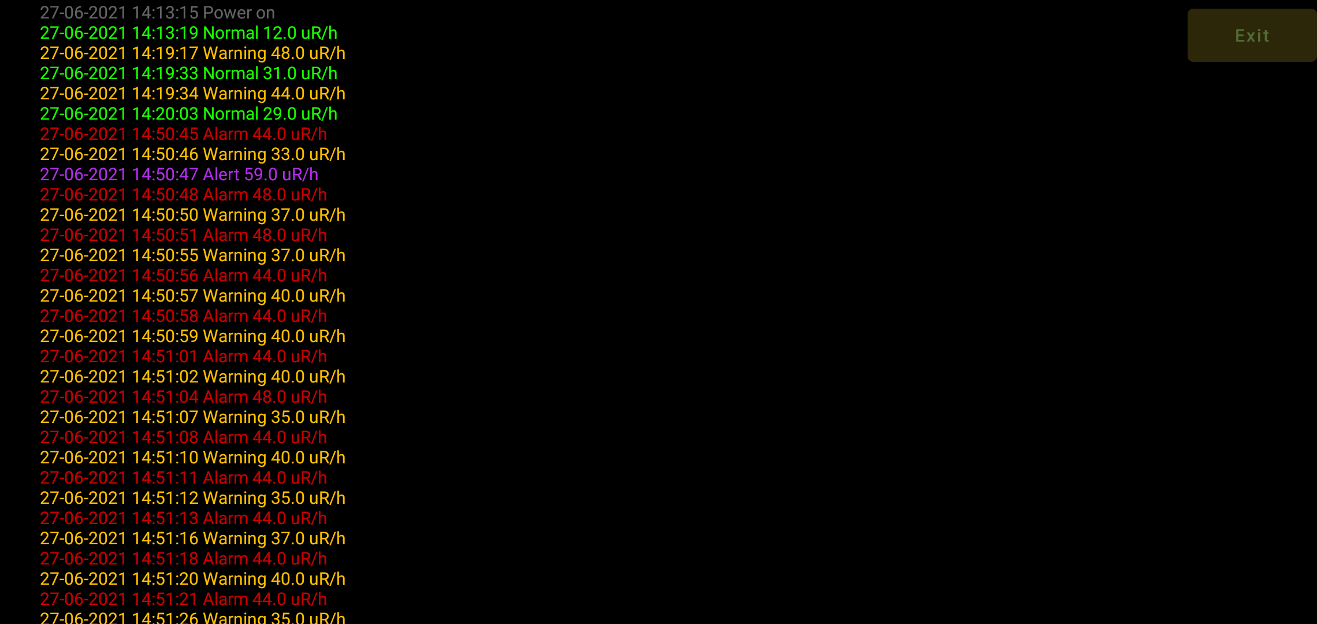
picture/Screenshot_20210627-153201.png
