Maniak003/DoZer/picture/Screenshot_20210723-102525.png

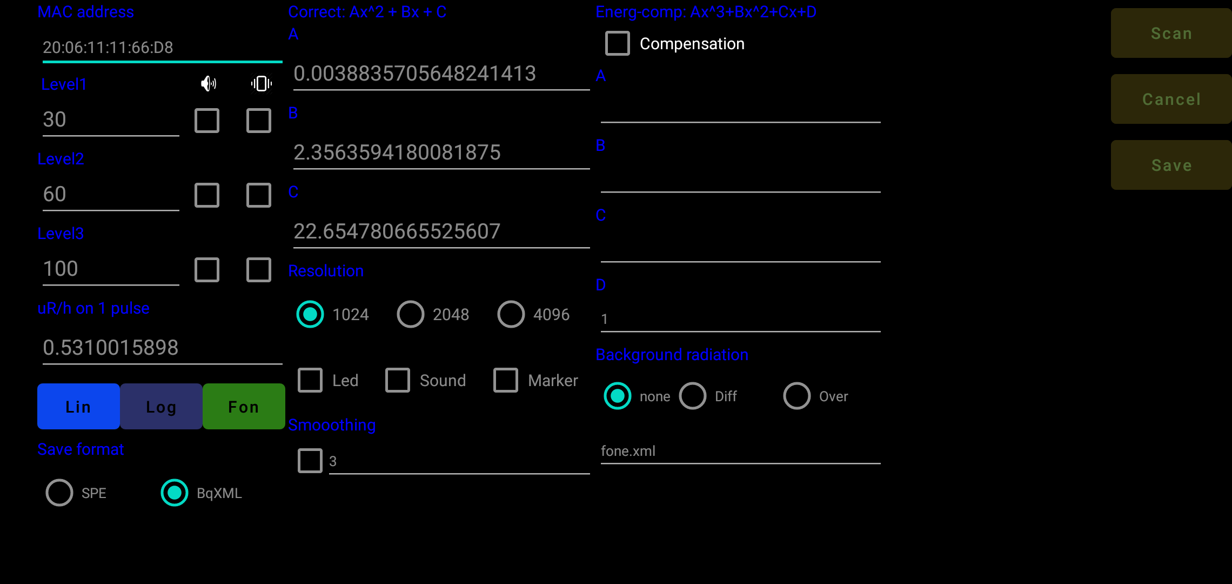
picture/Screenshot_20210723-102525.png
