Maniak003/DoZer/picture/Screenshot_20210905-000447.png

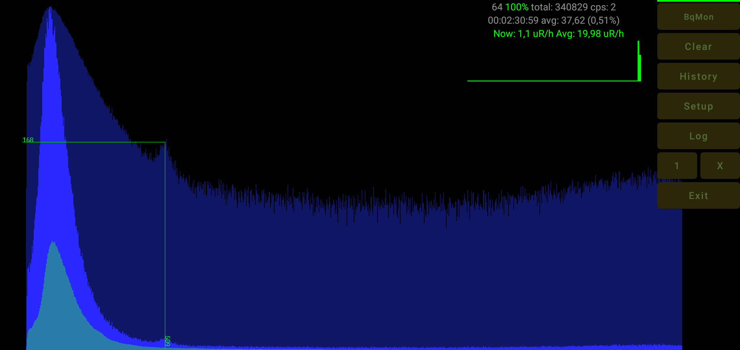
picture/Screenshot_20210905-000447.png
