Maniak003/DoZer/picture/Screenshot_20210913-154949.png

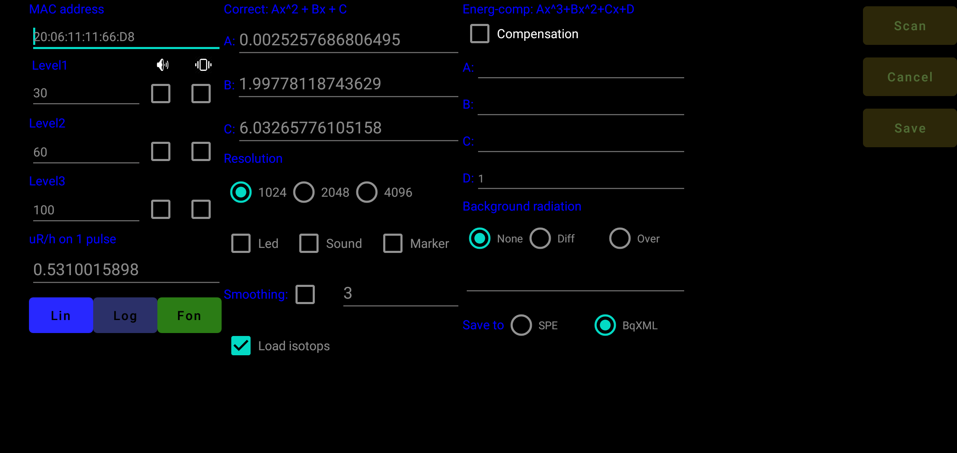
picture/Screenshot_20210913-154949.png
