Maniak003/DoZer/picture/Screenshot_20211011-080527.png

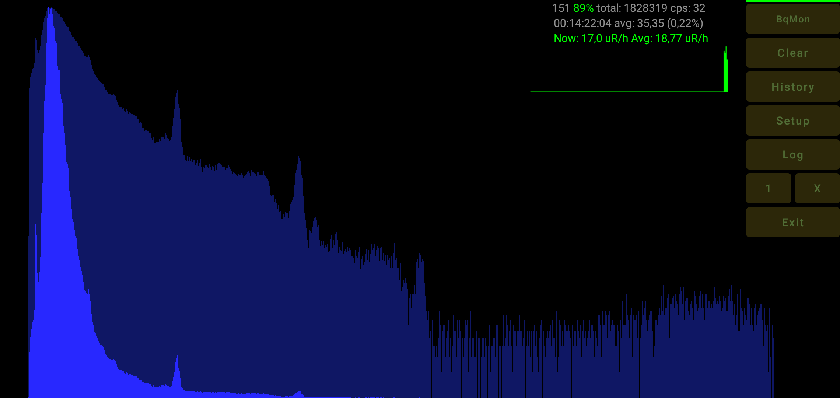
picture/Screenshot_20211011-080527.png
