Maniak003/DoZer/picture/Screenshot_20211024-135302.png

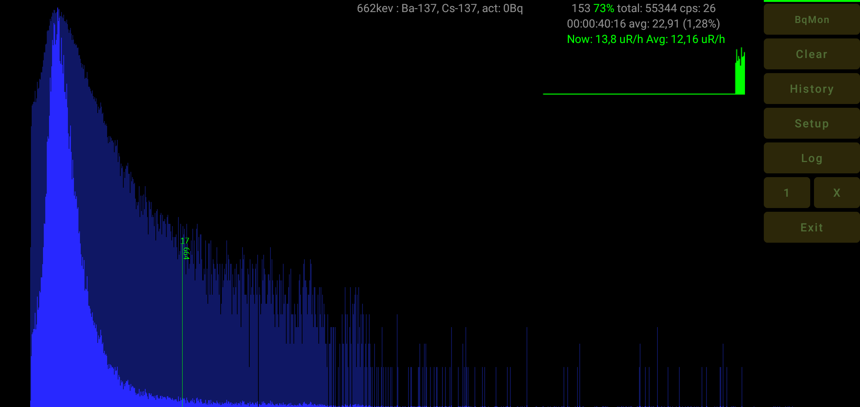
picture/Screenshot_20211024-135302.png
