Maniak003/DoZer/picture/Screenshot_20230306-181206.png

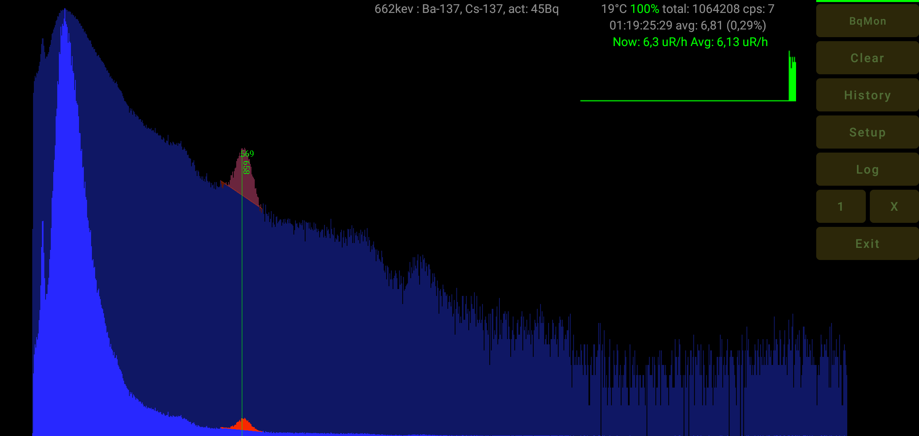
picture/Screenshot_20230306-181206.png
